joewing/q2/hardware/q2/pcb/q2/address.kicad_sch

## KiCad design hardware/q2/pcb/q2/address.kicad_sch (2024-12-15)

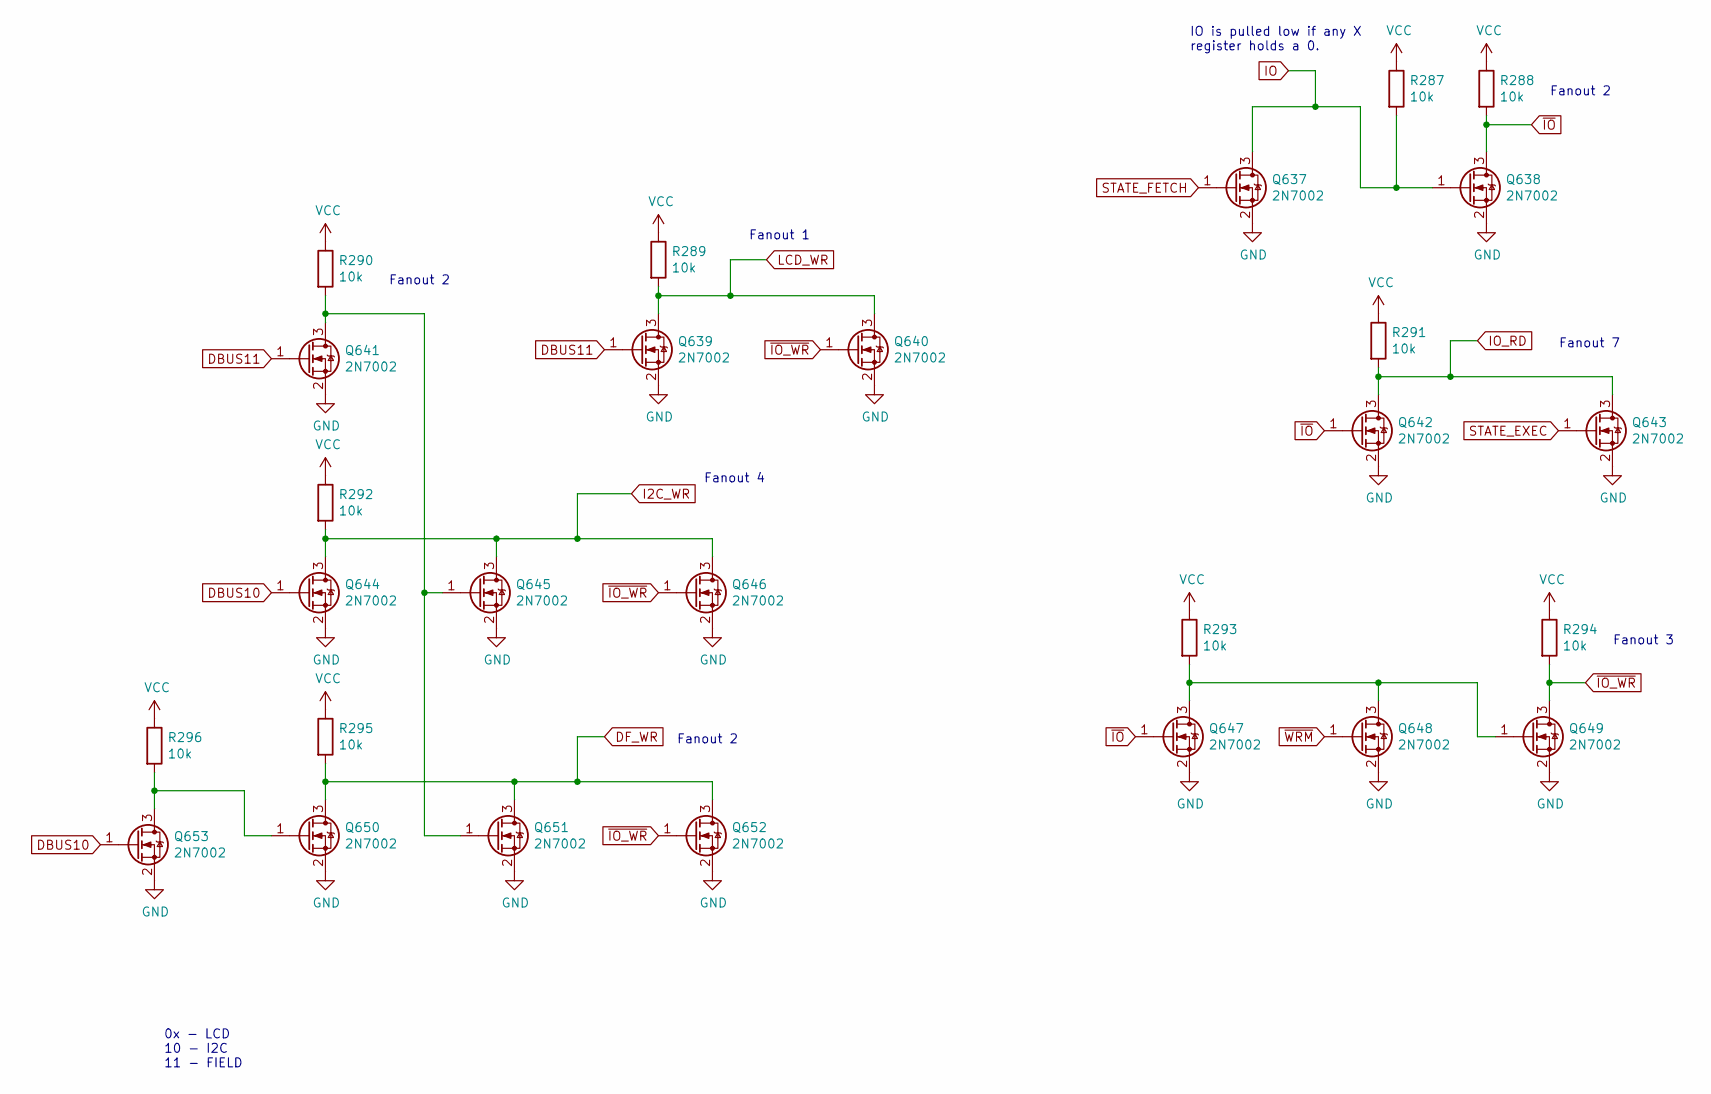
[picture p8: schematic address.kicad_sch]

Parts:
Q637, Q638, Q639, Q640, Q641, Q642, Q643, Q644, Q645, Q646, Q647, Q648, Q649, Q650, Q651, Q652, Q653: 2N7002; SOT-23; Part Number 2N7002; LCSC C181083
R287, R288, R289, R290, R291, R292, R293, R294, R295, R296: 10k; R_0603_1608Metric; Part Number 0603WAF1002T5E; LCSC C25804

Connections:
DBUS10: Q644.1 (G), Q653.1 (G)
DBUS11: Q639.1 (G), Q641.1 (G)
DF_WR: Q650.3 (D), Q651.3 (D), Q652.3 (D), R295.2
GND: Q637.2 (S), Q638.2 (S), Q639.2 (S), Q640.2 (S), Q641.2 (S), Q642.2 (S), Q643.2 (S), Q644.2 (S), Q645.2 (S), Q646.2 (S), Q647.2 (S), Q648.2 (S), Q649.2 (S), Q650.2 (S), Q651.2 (S), Q652.2 (S), Q653.2 (S)
I2C_WR: Q644.3 (D), Q645.3 (D), Q646.3 (D), R292.2
IO: Q637.3 (D), Q638.1 (G), R287.2
IO_RD: Q642.3 (D), Q643.3 (D), R291.2
LCD_WR: Q639.3 (D), Q640.3 (D), R289.2
unnamed: Q641.3 (D), Q645.1 (G), Q651.1 (G), R290.2
unnamed: Q647.3 (D), Q648.3 (D), Q649.1 (G), R293.2
unnamed: Q650.1 (G), Q653.3 (D), R296.2
STATE_EXEC: Q643.1 (G)
STATE_FETCH: Q637.1 (G)
VCC: R287.1, R288.1, R289.1, R290.1, R291.1, R292.1, R293.1, R294.1, R295.1, R296.1
~IO_WR: Q640.1 (G), Q646.1 (G), Q649.3 (D), Q652.1 (G), R294.2
~IO: Q638.3 (D), Q642.1 (G), Q647.1 (G), R288.2
~WRM: Q648.1 (G)

Notes on the sheet:
Fanout 2
Fanout 4
Fanout 3
0x - LCD 10 - I2C 11 - FIELD
IO is pulled low if any X register holds a 0.
Fanout 1
Fanout 7
