joewing/q2/hardware/q2/pcb/q2/alu.kicad_sch

## KiCad design hardware/q2/pcb/q2/alu.kicad_sch (2024-12-15)

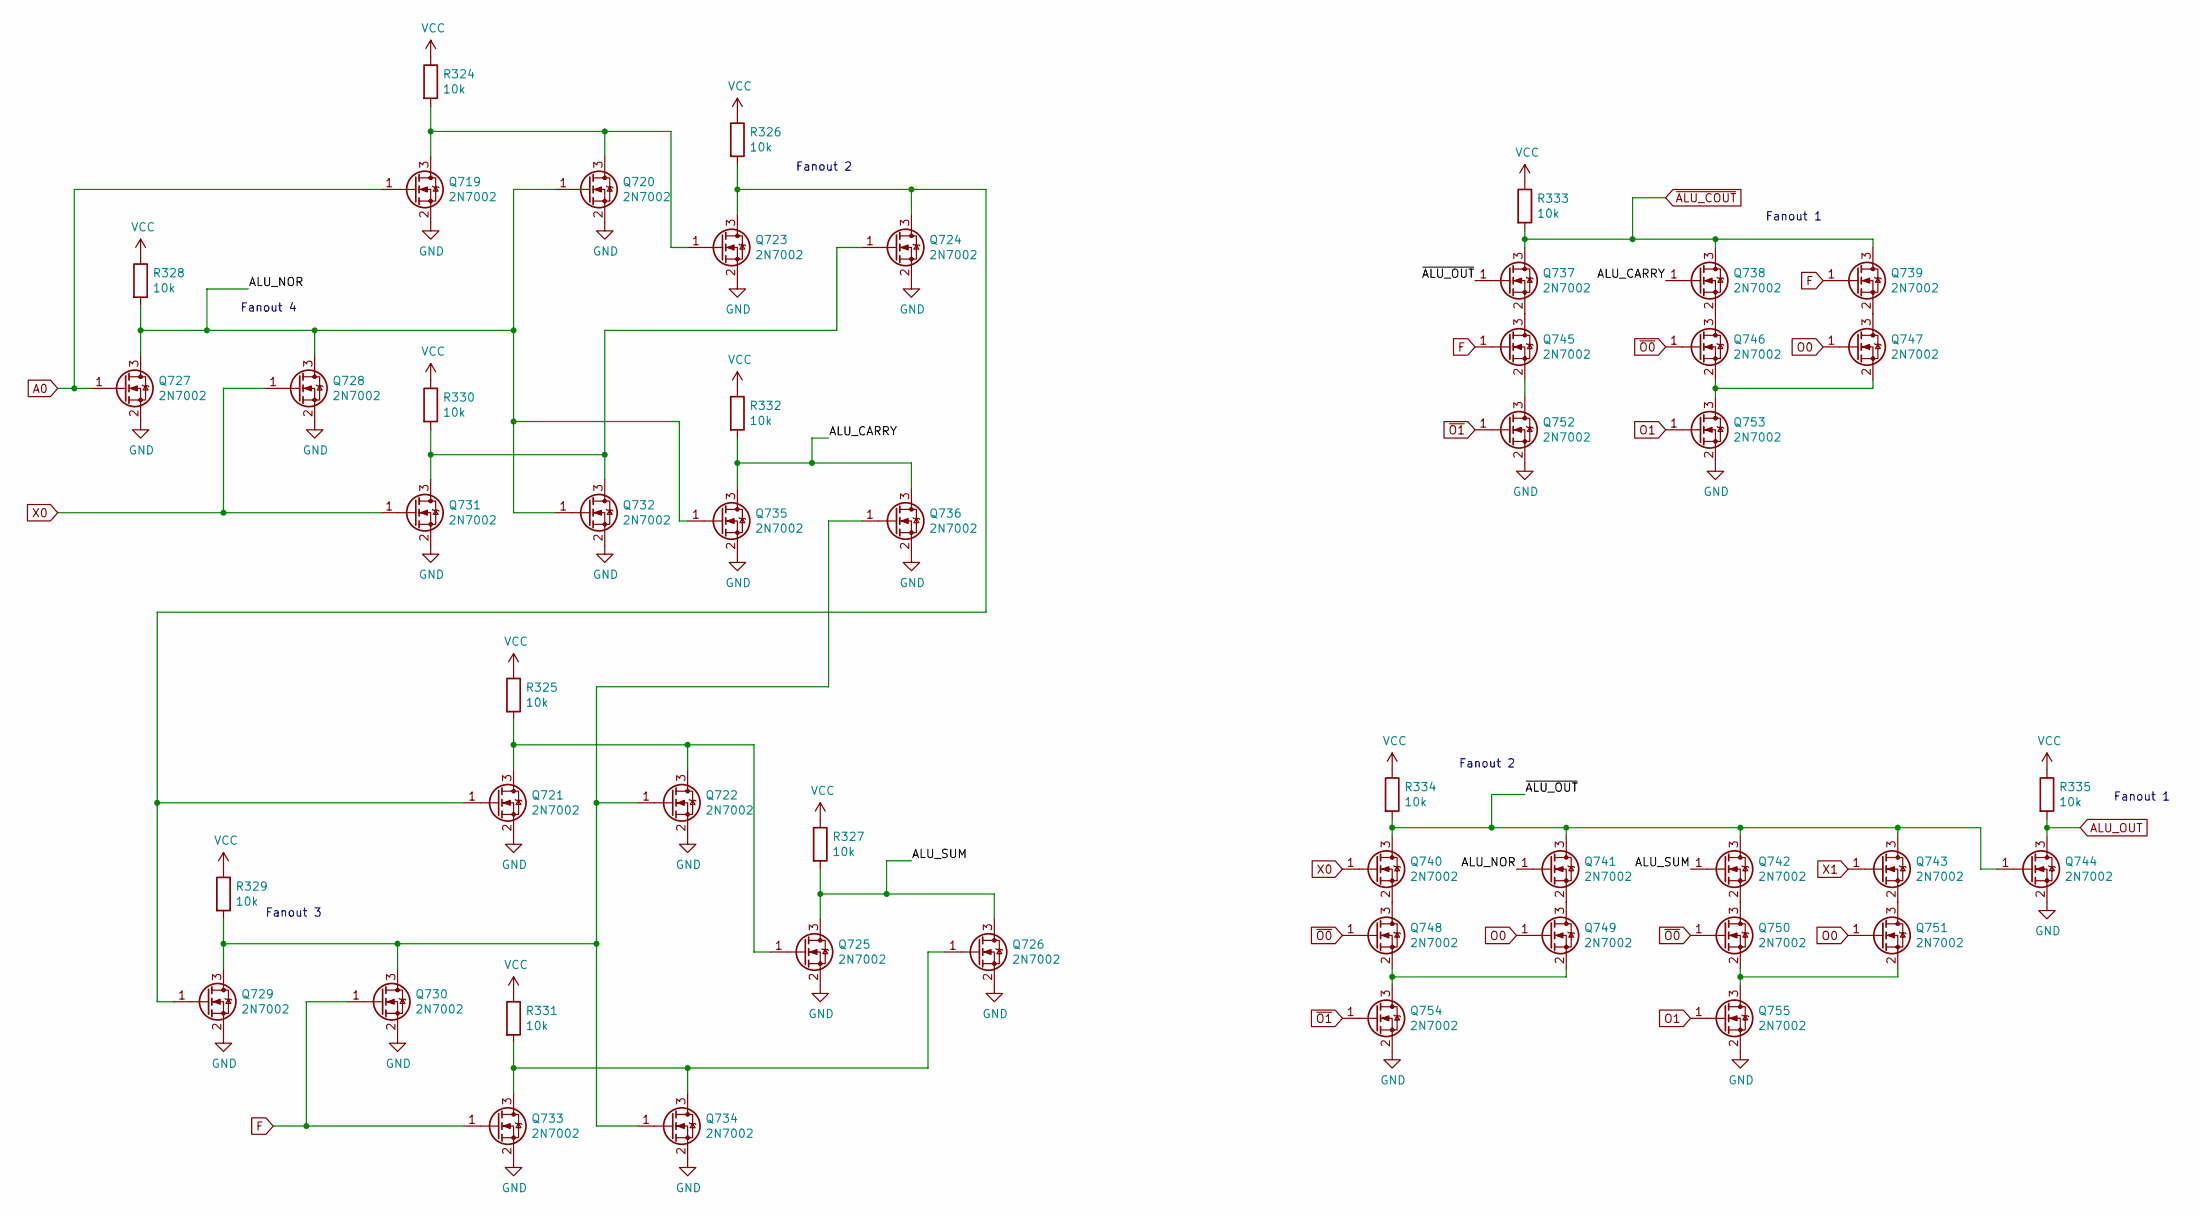
[picture p9: schematic alu.kicad_sch]

Parts:
Q719, Q720, Q721, Q722, Q723, Q724, Q725, Q726, Q727, Q728, Q729, Q730, Q731, Q732, Q733, Q734, Q735, Q736, Q737, Q738, Q739, Q740, Q741, Q742, Q743, Q744, Q745, Q746, Q747, Q748, Q749, Q750, Q751, Q752, Q753, Q754, Q755: 2N7002; SOT-23; Part Number 2N7002; LCSC C181083
R324, R325, R326, R327, R328, R329, R330, R331, R332, R333, R334, R335: 10k; R_0603_1608Metric; Part Number 0603WAF1002T5E; LCSC C25804

Connections:
A0: Q719.1 (G), Q727.1 (G)
ALU_CARRY: Q735.3 (D), Q736.3 (D), Q738.1 (G), R332.2
ALU_NOR: Q720.1 (G), Q727.3 (D), Q728.3 (D), Q732.1 (G), Q735.1 (G), Q741.1 (G), R328.2
ALU_OUT: Q744.3 (D), R335.2
ALU_SUM: Q725.3 (D), Q726.3 (D), Q742.1 (G), R327.2
F: Q730.1 (G), Q733.1 (G), Q739.1 (G), Q745.1 (G)
GND: Q719.2 (S), Q720.2 (S), Q721.2 (S), Q722.2 (S), Q723.2 (S), Q724.2 (S), Q725.2 (S), Q726.2 (S), Q727.2 (S), Q728.2 (S), Q729.2 (S), Q730.2 (S), Q731.2 (S), Q732.2 (S), Q733.2 (S), Q734.2 (S), Q735.2 (S), Q736.2 (S), Q744.2 (S), Q752.2 (S), Q753.2 (S), Q754.2 (S), Q755.2 (S)
unnamed: Q719.3 (D), Q720.3 (D), Q723.1 (G), R324.2
unnamed: Q721.1 (G), Q723.3 (D), Q724.3 (D), Q729.1 (G), R326.2
unnamed: Q721.3 (D), Q722.3 (D), Q725.1 (G), R325.2
unnamed: Q722.1 (G), Q729.3 (D), Q730.3 (D), Q734.1 (G), Q736.1 (G), R329.2
unnamed: Q724.1 (G), Q731.3 (D), Q732.3 (D), R330.2
unnamed: Q726.1 (G), Q733.3 (D), Q734.3 (D), R331.2
unnamed: Q737.2 (S), Q745.3 (D)
unnamed: Q738.2 (S), Q746.3 (D)
unnamed: Q739.2 (S), Q747.3 (D)
unnamed: Q740.2 (S), Q748.3 (D)
unnamed: Q741.2 (S), Q749.3 (D)
unnamed: Q742.2 (S), Q750.3 (D)
unnamed: Q743.2 (S), Q751.3 (D)
unnamed: Q745.2 (S), Q752.3 (D)
unnamed: Q746.2 (S), Q747.2 (S), Q753.3 (D)
unnamed: Q748.2 (S), Q749.2 (S), Q754.3 (D)
unnamed: Q750.2 (S), Q751.2 (S), Q755.3 (D)
O0: Q747.1 (G), Q749.1 (G), Q751.1 (G)
O1: Q753.1 (G), Q755.1 (G)
VCC: R324.1, R325.1, R326.1, R327.1, R328.1, R329.1, R330.1, R331.1, R332.1, R333.1, R334.1, R335.1
X0: Q728.1 (G), Q731.1 (G), Q740.1 (G)
X1: Q743.1 (G)
~ALU_COUT: Q737.3 (D), Q738.3 (D), Q739.3 (D), R333.2
~ALU_OUT: Q737.1 (G), Q740.3 (D), Q741.3 (D), Q742.3 (D), Q743.3 (D), Q744.1 (G), R334.2
~O0: Q746.1 (G), Q748.1 (G), Q750.1 (G)
~O1: Q752.1 (G), Q754.1 (G)

Notes on the sheet:
Fanout 2
Fanout 1
Fanout 3
Fanout 4
