joewing/q2/hardware/q2/pcb/q2/areg.kicad_sch

## KiCad design hardware/q2/pcb/q2/areg.kicad_sch (2024-12-15)

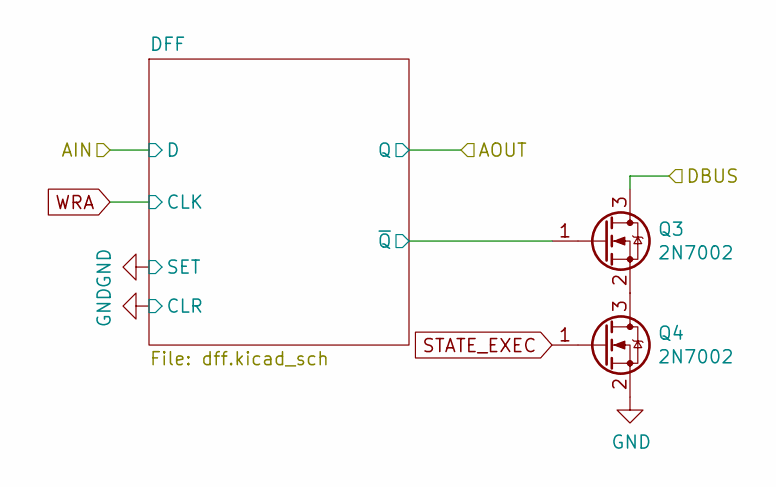
[picture p10: schematic areg.kicad_sch]

Parts:
Q3, Q4: 2N7002; SOT-23; Part Number 2N7002; LCSC C181083

Connections:
DBUS: Q3.3 (D)
GND: Q4.2 (S)
unnamed: Q3.2 (S), Q4.3 (D)
STATE_EXEC: Q4.1 (G)
~Q: Q3.1 (G)
