joewing/q2/hardware/q2/pcb/q2/clock.kicad_sch

## KiCad design hardware/q2/pcb/q2/clock.kicad_sch (2024-12-15)

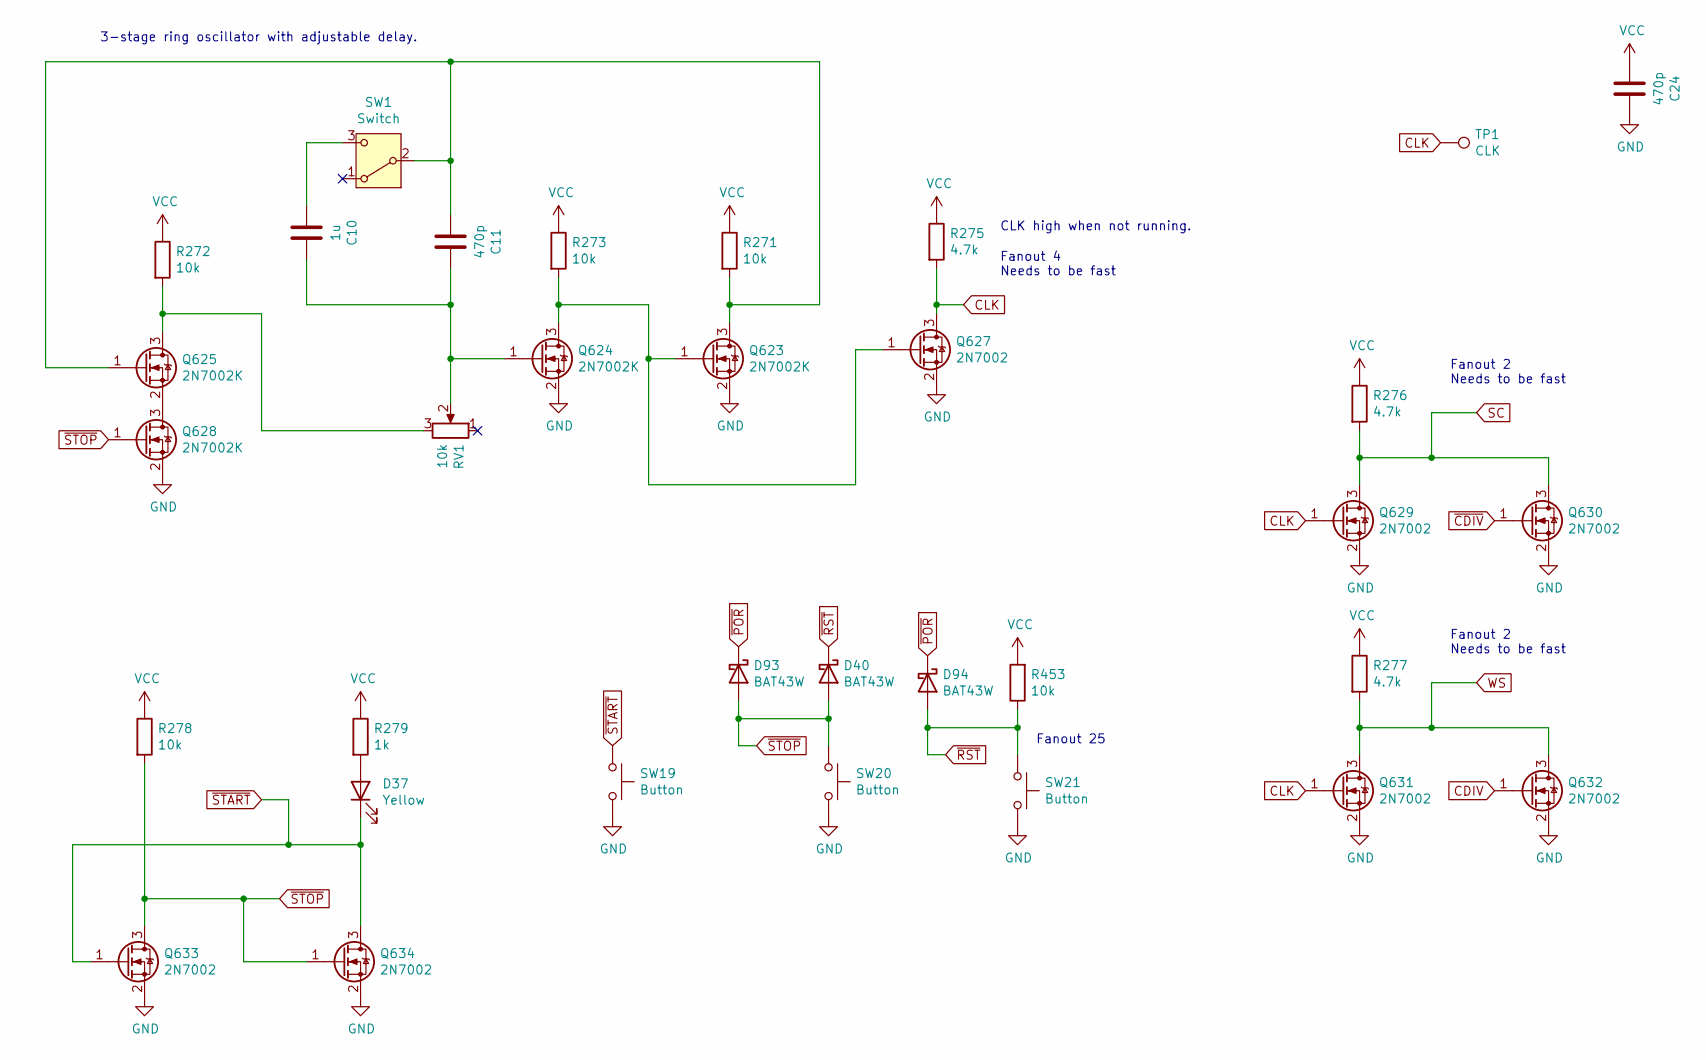
[picture p11: schematic clock.kicad_sch]

Parts:
C10: 1u; C_0805_2012Metric; Part Number CL21B105KBFNNNE; LCSC C28323
C11, C24: 470p; C_0805_2012Metric; Part Number 0805B471K500NT; LCSC C1743
D37: Yellow; LED_0805_2012Metric; Part Number 17-21SUYC/TR8; LCSC C2296
D40, D93, D94: BAT43W; D_SOD-123; Part Number BAT43W; LCSC C19167
Q623, Q624, Q625, Q628: 2N7002K; SOT-23; Part Number 2N7002K; LCSC C181083
Q627, Q629, Q630, Q631, Q632, Q633, Q634: 2N7002; SOT-23; Part Number 2N7002; LCSC C181083
R271, R272, R273, R278, R453: 10k; R_0603_1608Metric; Part Number 0603WAF1002T5E; LCSC C25804
R275, R276, R277: 4.7k; R_0603_1608Metric; Part Number 0603WAF4701T5E; LCSC C23162
R279: 1k; R_0603_1608Metric; Part Number 0603WAF1001T5E; LCSC C21190
RV1: 10k; Potentiometer_Bourns_3386P_Vertical; Part Number 3386P-1-103LF; LCSC C116281
SW1: Switch; TA-3524S-A2; Part Number TA-3524S-A2; LCSC C514017
SW19, SW20, SW21: Button; SW_SPST_PTS645; Part Number UK-B0228-G5-160-JZ; LCSC C620316
TP1: CLK; TestPoint_Loop_D2.50mm_Drill1.0mm

Connections:
CDIV: Q632.1 (G)
CLK: Q627.3 (D), Q629.1 (G), Q631.1 (G), R275.2, TP1.1
GND: C24.1, Q623.2 (S), Q624.2 (S), Q627.2 (S), Q628.2 (S), Q629.2 (S), Q630.2 (S), Q631.2 (S), Q632.2 (S), Q633.2 (S), Q634.2 (S), SW19.2, SW20.2, SW21.2
unnamed: C10.1, C11.1, Q624.1 (G), RV1.2
unnamed: C10.2, SW1.3 (C)
unnamed: C11.2, Q623.3 (D), Q625.1 (G), R271.2, SW1.2 (B)
unnamed: D37.2 (A), R279.2
unnamed: Q623.1 (G), Q624.3 (D), Q627.1 (G), R273.2
unnamed: Q625.2 (S), Q628.3 (D)
unnamed: Q625.3 (D), R272.2, RV1.3
SC: Q629.3 (D), Q630.3 (D), R276.2
VCC: C24.2, R271.1, R272.1, R273.1, R275.1, R276.1, R277.1, R278.1, R279.1, R453.2
WS: Q631.3 (D), Q632.3 (D), R277.2
~CDIV: Q630.1 (G)
~POR: D93.1 (K), D94.1 (K)
~RST: D40.1 (K), D94.2 (A), R453.1, SW21.1
~START: D37.1 (K), Q633.1 (G), Q634.3 (D), SW19.1
~STOP: D40.2 (A), D93.2 (A), Q628.1 (G), Q633.3 (D), Q634.1 (G), R278.2, SW20.1

Notes on the sheet:
Fanout 4 Needs to be fast
CLK high when not running.
Fanout 25
Fanout 2 Needs to be fast
3-stage ring oscillator with adjustable delay.
