joewing/q2/hardware/q2/pcb/q2/control.kicad_sch

## KiCad design hardware/q2/pcb/q2/control.kicad_sch (2024-12-15)

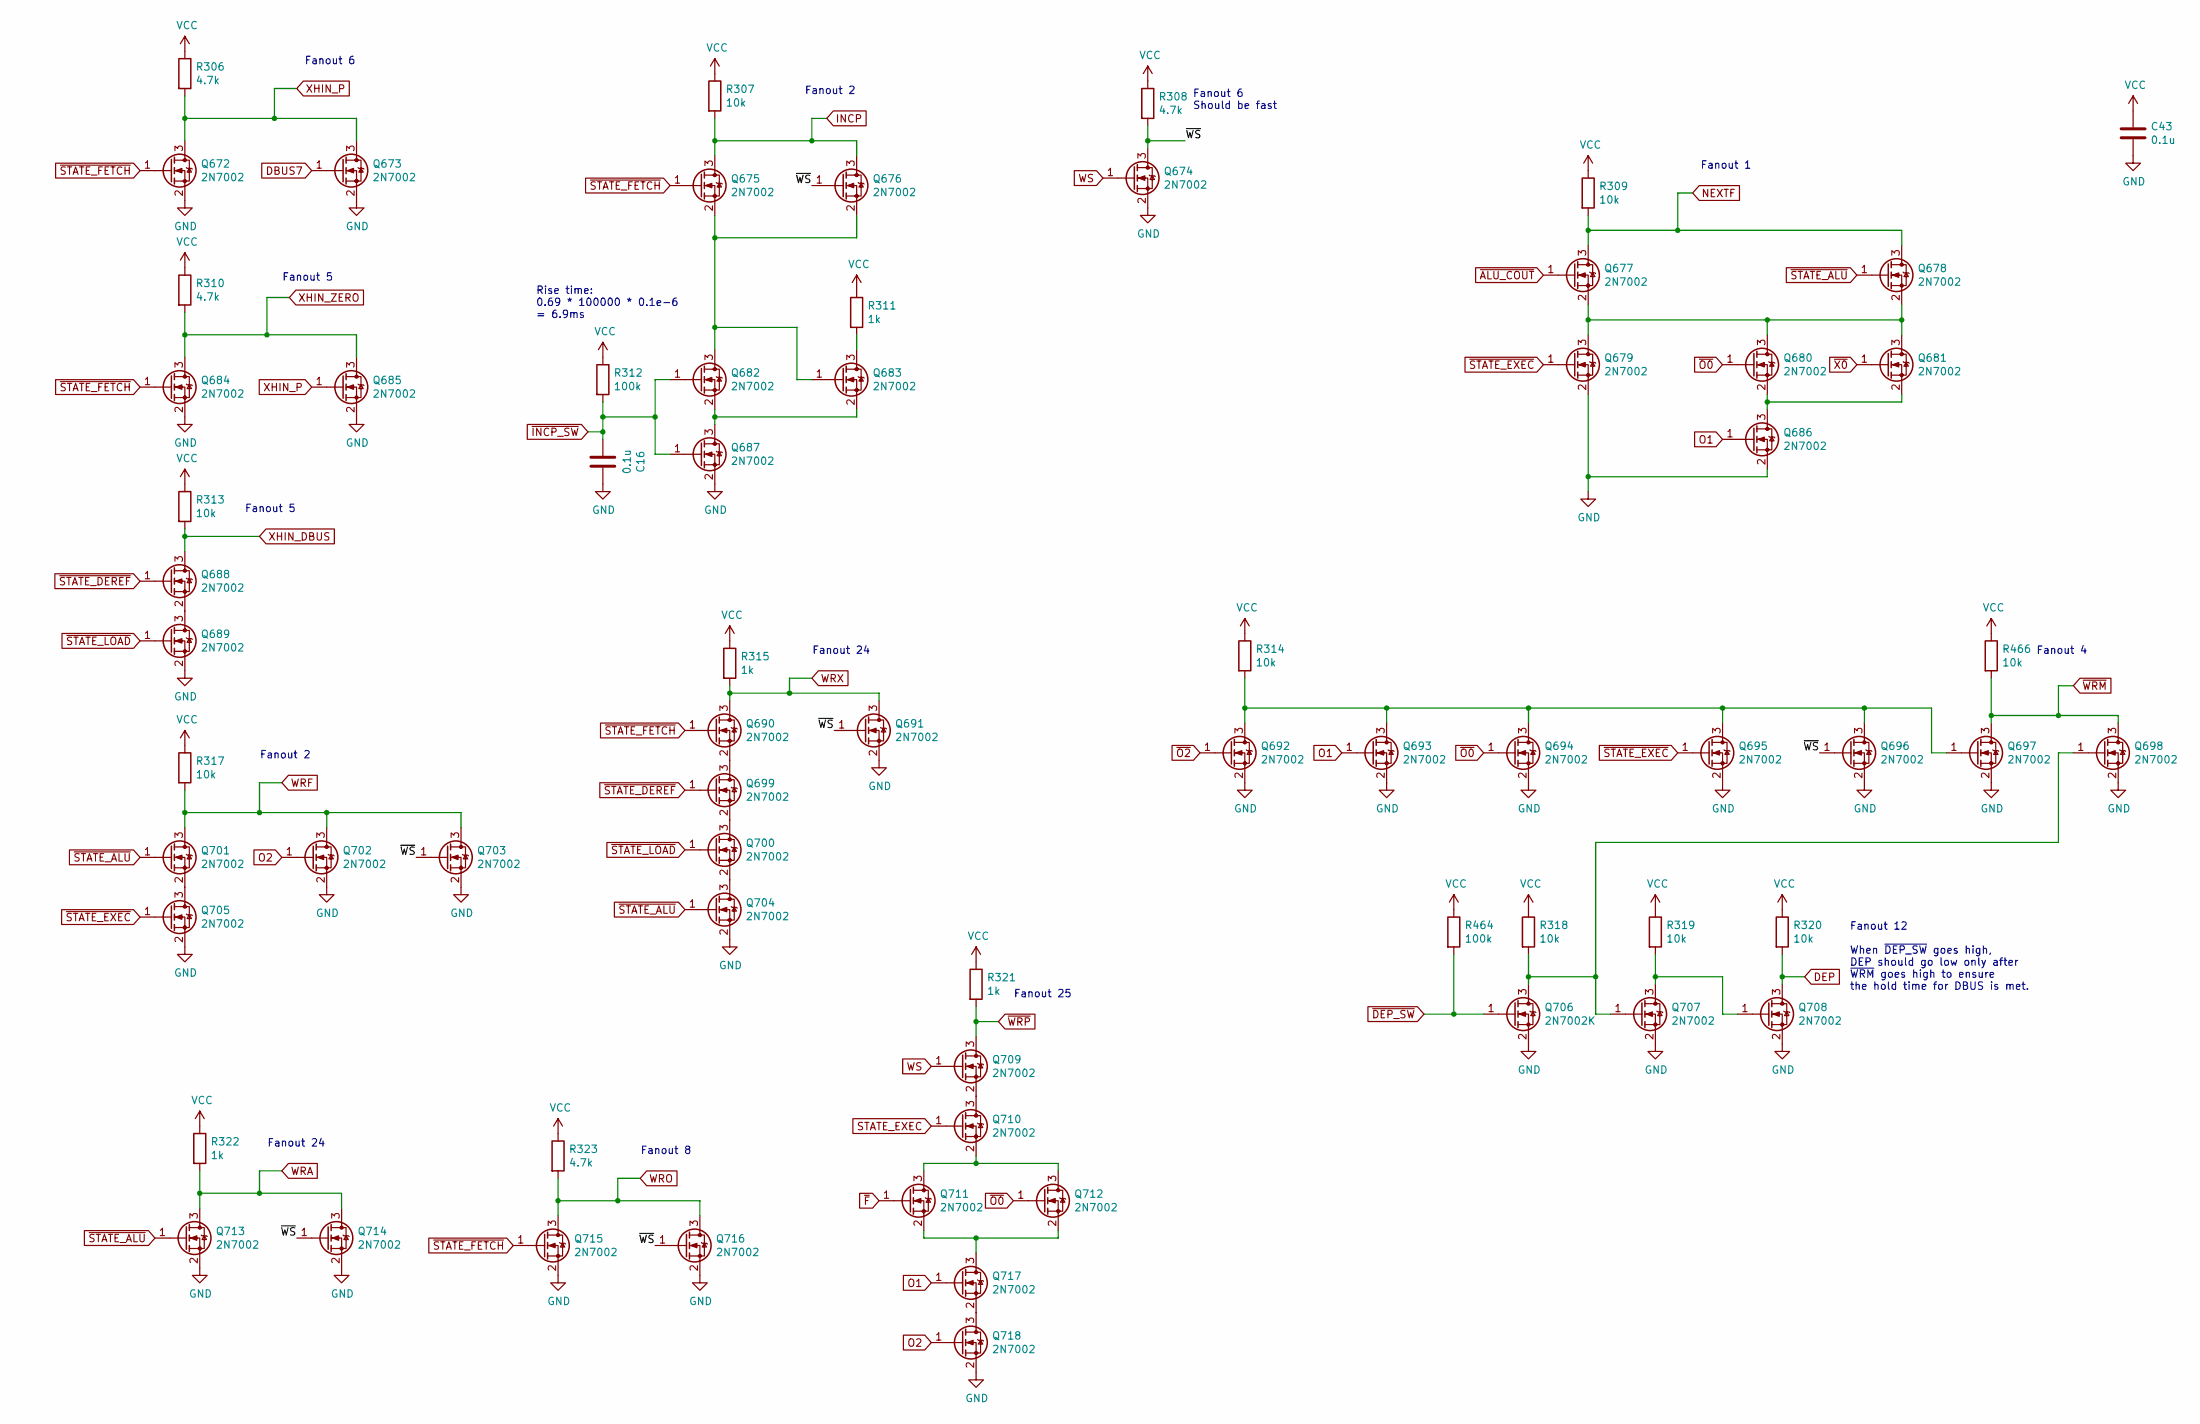
[picture p12: schematic control.kicad_sch]

Parts:
C16, C43: 0.1u; C_0805_2012Metric; Part Number CC0805KRX7R9BB104; LCSC C49678
Q672, Q673, Q674, Q675, Q676, Q677, Q678, Q679, Q680, Q681, Q682, Q683, Q684, Q685, Q686, Q687, Q688, Q689, Q690, Q691, Q692, Q693, Q694, Q695, Q696, Q697, Q698, Q699, Q700, Q701, Q702, Q703, Q704, Q705, Q707, Q708, Q709, Q710, Q711, Q712, Q713, Q714, Q715, Q716, Q717, Q718: 2N7002; SOT-23; Part Number 2N7002; LCSC C181083
Q706: 2N7002K; SOT-23; Part Number 2N7002K; LCSC C181083
R306, R308, R310, R323: 4.7k; R_0603_1608Metric; Part Number 0603WAF4701T5E; LCSC C23162
R307, R309, R313, R314, R317, R318, R319, R320, R466: 10k; R_0603_1608Metric; Part Number 0603WAF1002T5E; LCSC C25804
R311, R315, R321, R322: 1k; R_0603_1608Metric; Part Number 0603WAF1001T5E; LCSC C21190
R312, R464: 100k; R_0603_1608Metric; Part Number 0603WAF1003T5E; LCSC C25803

Connections:
DBUS7: Q673.1 (G)
DEP: Q708.3 (D), R320.2
GND: C16.1, C43.2, Q672.2 (S), Q673.2 (S), Q674.2 (S), Q679.2 (S), Q684.2 (S), Q685.2 (S), Q686.2 (S), Q687.2 (S), Q689.2 (S), Q691.2 (S), Q692.2 (S), Q693.2 (S), Q694.2 (S), Q695.2 (S), Q696.2 (S), Q697.2 (S), Q698.2 (S), Q702.2 (S), Q703.2 (S), Q704.2 (S), Q705.2 (S), Q706.2 (S), Q707.2 (S), Q708.2 (S), Q713.2 (S), Q714.2 (S), Q715.2 (S), Q716.2 (S), Q718.2 (S)
INCP: Q675.3 (D), Q676.3 (D), R307.2
NEXTF: Q677.3 (D), Q678.3 (D), R309.2
unnamed: Q675.2 (S), Q676.2 (S), Q682.3 (D), Q683.1 (G)
unnamed: Q677.2 (S), Q678.2 (S), Q679.3 (D), Q680.3 (D), Q681.3 (D)
unnamed: Q680.2 (S), Q681.2 (S), Q686.3 (D)
unnamed: Q682.2 (S), Q683.2 (S), Q687.3 (D)
unnamed: Q683.3 (D), R311.2
unnamed: Q688.2 (S), Q689.3 (D)
unnamed: Q690.2 (S), Q699.3 (D)
unnamed: Q692.3 (D), Q693.3 (D), Q694.3 (D), Q695.3 (D), Q696.3 (D), Q697.1 (G), R314.2
unnamed: Q698.1 (G), Q706.3 (D), Q707.1 (G), R318.2
unnamed: Q699.2 (S), Q700.3 (D)
unnamed: Q700.2 (S), Q704.3 (D)
unnamed: Q701.2 (S), Q705.3 (D)
unnamed: Q707.3 (D), Q708.1 (G), R319.2
unnamed: Q709.2 (S), Q710.3 (D)
unnamed: Q710.2 (S), Q711.3 (D), Q712.3 (D)
unnamed: Q711.2 (S), Q712.2 (S), Q717.3 (D)
unnamed: Q717.2 (S), Q718.3 (D)
O1: Q686.1 (G), Q693.1 (G), Q717.1 (G)
O2: Q702.1 (G), Q718.1 (G)
STATE_EXEC: Q710.1 (G)
VCC: C43.1, R306.1, R307.1, R308.1, R309.1, R310.1, R311.1, R312.1, R313.1, R314.1, R315.1, R317.1, R318.1, R319.1, R320.1, R321.1, R322.1, R323.1, R464.1, R466.1
WRA: Q713.3 (D), Q714.3 (D), R322.2
WRF: Q701.3 (D), Q702.3 (D), Q703.3 (D), R317.2
WRO: Q715.3 (D), Q716.3 (D), R323.2
WRX: Q690.3 (D), Q691.3 (D), R315.2
WS: Q674.1 (G), Q709.1 (G)
XHIN_DBUS: Q688.3 (D), R313.2
XHIN_P: Q672.3 (D), Q673.3 (D), Q685.1 (G), R306.2
XHIN_ZERO: Q684.3 (D), Q685.3 (D), R310.2
~ALU_COUT: Q677.1 (G)
~DEP_SW: Q706.1 (G), R464.2
~F: Q711.1 (G)
~INCP_SW: C16.2, Q682.1 (G), Q687.1 (G), R312.2
~O0: Q680.1 (G), Q694.1 (G), Q712.1 (G)
~O2: Q692.1 (G)
~STATE_ALU: Q678.1 (G), Q701.1 (G), Q704.1 (G), Q713.1 (G)
~STATE_DEREF: Q688.1 (G), Q699.1 (G)
~STATE_EXEC: Q679.1 (G), Q695.1 (G), Q705.1 (G)
~STATE_FETCH: Q672.1 (G), Q675.1 (G), Q684.1 (G), Q690.1 (G), Q715.1 (G)
~STATE_LOAD: Q689.1 (G), Q700.1 (G)
~WRM: Q697.3 (D), Q698.3 (D), R466.2
~WRP: Q709.3 (D), R321.2
~WS: Q674.3 (D), Q676.1 (G), Q691.1 (G), Q696.1 (G), Q703.1 (G), Q714.1 (G), Q716.1 (G), R308.2
~X0: Q681.1 (G)

Notes on the sheet:
Fanout 25
Fanout 4
Fanout 5
Fanout 24
Fanout 12 When ~{DEP_SW} goes high, DEP should go low only after ~{WRM} goes high to ensure the hold time for DBUS is met.
Fanout 2
Fanout 6 Should be fast
Fanout 6
Fanout 8
Rise time: 0.69 * 100000 * 0.1e-6 = 6.9ms
Fanout 1
