joewing/q2/hardware/q2/pcb/q2/decoder.kicad_sch

## KiCad design hardware/q2/pcb/q2/decoder.kicad_sch (2024-12-15)

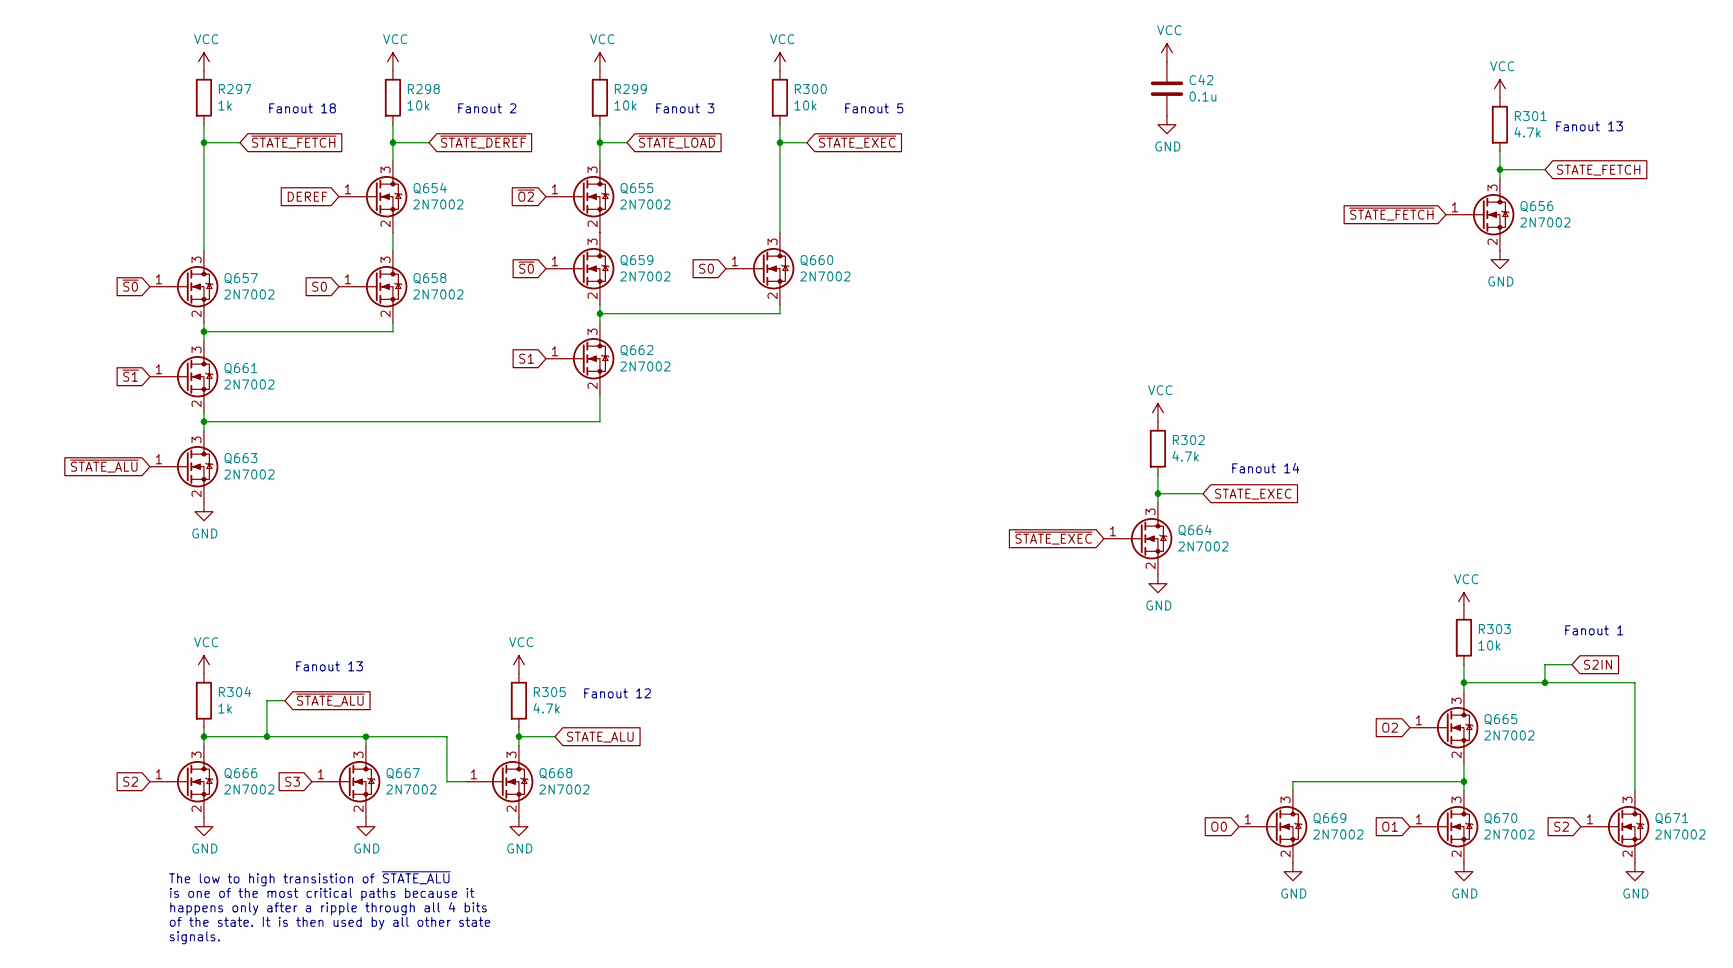
[picture p13: schematic decoder.kicad_sch]

Parts:
C42: 0.1u; C_0805_2012Metric; Part Number CC0805KRX7R9BB104; LCSC C49678
Q654, Q655, Q656, Q657, Q658, Q659, Q660, Q661, Q662, Q663, Q664, Q665, Q666, Q667, Q668, Q669, Q670, Q671: 2N7002; SOT-23; Part Number 2N7002; LCSC C181083
R297, R304: 1k; R_0603_1608Metric; Part Number 0603WAF1001T5E; LCSC C21190
R298, R299, R300, R303: 10k; R_0603_1608Metric; Part Number 0603WAF1002T5E; LCSC C25804
R301, R302, R305: 4.7k; R_0603_1608Metric; Part Number 0603WAF4701T5E; LCSC C23162

Connections:
DEREF: Q654.1 (G)
GND: C42.2, Q656.2 (S), Q663.2 (S), Q664.2 (S), Q666.2 (S), Q667.2 (S), Q668.2 (S), Q669.2 (S), Q670.2 (S), Q671.2 (S)
unnamed: Q654.2 (S), Q658.3 (D)
unnamed: Q655.2 (S), Q659.3 (D)
unnamed: Q657.2 (S), Q658.2 (S), Q661.3 (D)
unnamed: Q659.2 (S), Q660.2 (S), Q662.3 (D)
unnamed: Q661.2 (S), Q662.2 (S), Q663.3 (D)
unnamed: Q665.2 (S), Q669.3 (D), Q670.3 (D)
O0: Q669.1 (G)
O1: Q670.1 (G)
O2: Q665.1 (G)
S0: Q658.1 (G), Q660.1 (G)
S1: Q662.1 (G)
S2: Q666.1 (G), Q671.1 (G)
S2IN: Q665.3 (D), Q671.3 (D), R303.2
S3: Q667.1 (G)
STATE_ALU: Q668.3 (D), R305.2
STATE_EXEC: Q664.3 (D), R302.2
STATE_FETCH: Q656.3 (D), R301.2
VCC: C42.1, R297.1, R298.1, R299.1, R300.1, R301.1, R302.1, R303.1, R304.1, R305.1
~O2: Q655.1 (G)
~S0: Q657.1 (G), Q659.1 (G)
~S1: Q661.1 (G)
~STATE_ALU: Q663.1 (G), Q666.3 (D), Q667.3 (D), Q668.1 (G), R304.2
~STATE_DEREF: Q654.3 (D), R298.2
~STATE_EXEC: Q660.3 (D), Q664.1 (G), R300.2
~STATE_FETCH: Q656.1 (G), Q657.3 (D), R297.2
~STATE_LOAD: Q655.3 (D), R299.2

Notes on the sheet:
Fanout 13
Fanout 14
Fanout 12
Fanout 2
Fanout 1
The low to high transistion of ~{STATE_ALU} is one of the most critical paths because it happens only after a ripple through all 4 bits of the state. It is then used by all other state signals.
Fanout 5
Fanout 3
Fanout 18
