joewing/q2/hardware/q2/pcb/q2/dff.kicad_sch

## KiCad design hardware/q2/pcb/q2/dff.kicad_sch (2024-12-15)

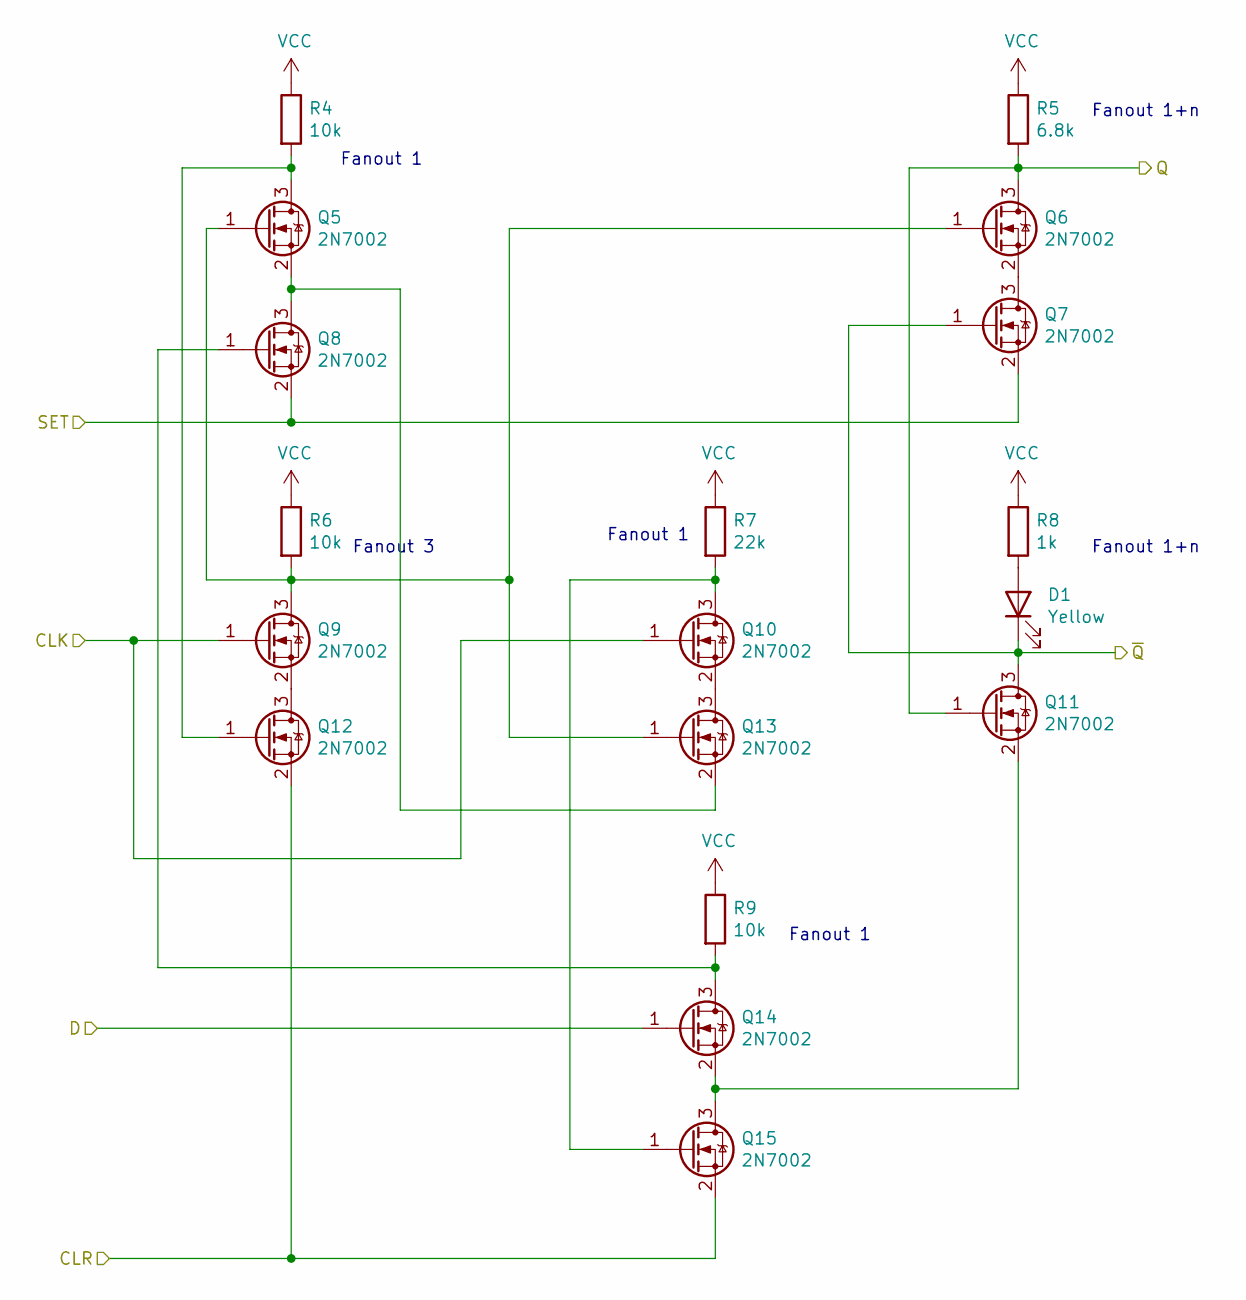
[picture p14: schematic dff.kicad_sch]

Parts:
D1: Yellow; LED_0805_2012Metric; Part Number 17-21SUYC/TR8; LCSC C2296
Q5, Q6, Q7, Q8, Q9, Q10, Q11, Q12, Q13, Q14, Q15: 2N7002; SOT-23; Part Number 2N7002; LCSC C181083
R4, R6, R9: 10k; R_0603_1608Metric; Part Number 0603WAF1002T5E; LCSC C25804
R5: 6.8k; R_0603_1608Metric; Part Number 0603WAF6801T5E; LCSC C23212
R7: 22k; R_0603_1608Metric; Part Number 0603WAF2202T5E; LCSC C31850
R8: 1k; R_0603_1608Metric; Part Number 0603WAF1001T5E; LCSC C21190

Connections:
CLK: Q9.1 (G), Q10.1 (G)
CLR: Q12.2 (S), Q15.2 (S)
D: Q14.1 (G)
unnamed: D1.2 (A), R8.2
unnamed: Q6.2 (S), Q7.3 (D)
unnamed: Q10.2 (S), Q13.3 (D)
unnamed: Q10.3 (D), Q15.1 (G), R7.2
unnamed: Q11.2 (S), Q14.2 (S), Q15.3 (D)
unnamed: Q5.3 (D), Q12.1 (G), R4.2
unnamed: Q9.2 (S), Q12.3 (D)
unnamed: Q5.1 (G), Q6.1 (G), Q9.3 (D), Q13.1 (G), R6.2
unnamed: Q5.2 (S), Q8.3 (D), Q13.2 (S)
unnamed: Q8.1 (G), Q14.3 (D), R9.2
Q: Q6.3 (D), Q11.1 (G), R5.2
SET: Q7.2 (S), Q8.2 (S)
VCC: R4.1, R5.1, R6.1, R7.1, R8.1, R9.1
~Q: D1.1 (K), Q7.1 (G), Q11.3 (D)

Notes on the sheet:
Fanout 1+n
Fanout 1
Fanout 3
