joewing/q2/hardware/q2/pcb/q2/field.kicad_sch

## KiCad design hardware/q2/pcb/q2/field.kicad_sch (2024-12-15)

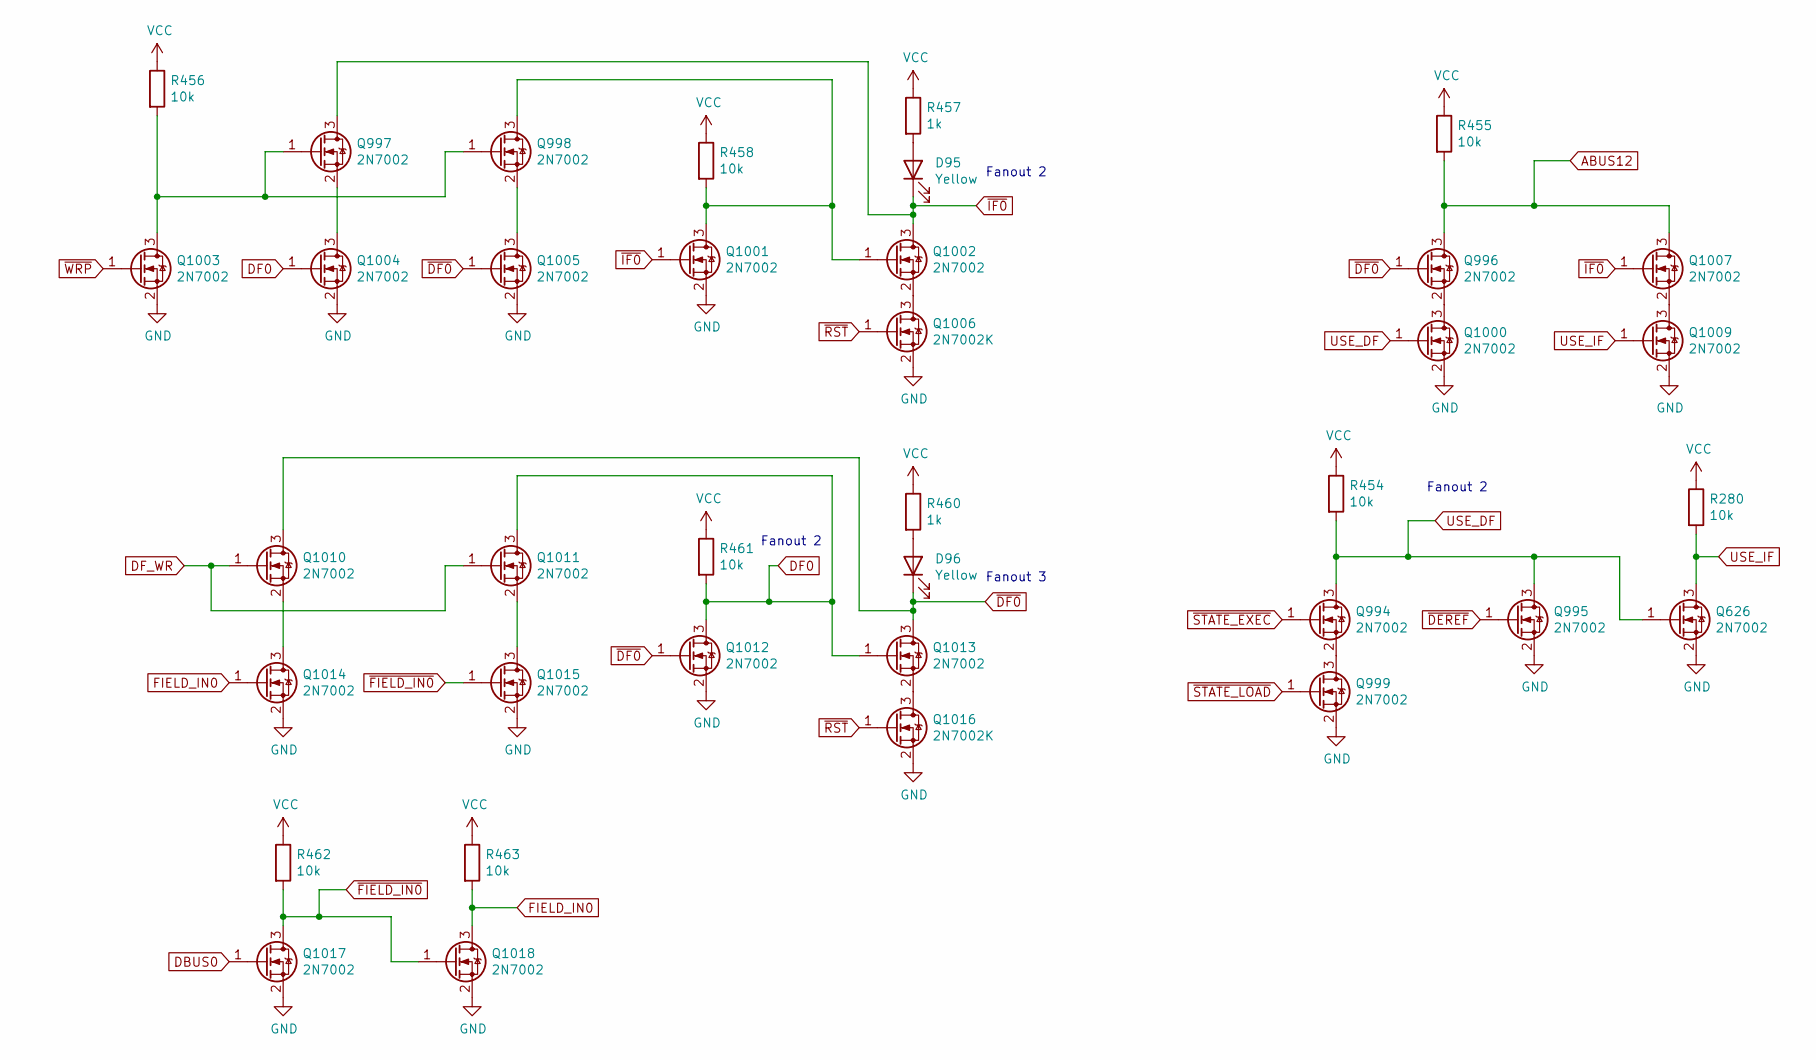
[picture p15: schematic field.kicad_sch]

Parts:
D95, D96: Yellow; LED_0805_2012Metric; Part Number 17-21SUYC/TR8; LCSC C2296
Q626, Q994, Q995, Q996, Q997, Q998, Q999, Q1000, Q1001, Q1002, Q1003, Q1004, Q1005, Q1007, Q1009, Q1010, Q1011, Q1012, Q1013, Q1014, Q1015, Q1017, Q1018: 2N7002; SOT-23; Part Number 2N7002; LCSC C181083
Q1006, Q1016: 2N7002K; SOT-23; Part Number 2N7002K; LCSC C181083
R280, R454, R455, R456, R458, R461, R462, R463: 10k; R_0603_1608Metric; Part Number 0603WAF1002T5E; LCSC C25804
R457, R460: 1k; R_0603_1608Metric; Part Number 0603WAF1001T5E; LCSC C21190

Connections:
ABUS12: Q996.3 (D), Q1007.3 (D), R455.2
DBUS0: Q1017.1 (G)
DF0: Q1004.1 (G), Q1011.3 (D), Q1012.3 (D), Q1013.1 (G), R461.2
DF_WR: Q1010.1 (G), Q1011.1 (G)
FIELD_IN0: Q1014.1 (G), Q1018.3 (D), R463.2
GND: Q626.2 (S), Q995.2 (S), Q999.2 (S), Q1000.2 (S), Q1001.2 (S), Q1003.2 (S), Q1004.2 (S), Q1005.2 (S), Q1006.2 (S), Q1009.2 (S), Q1012.2 (S), Q1014.2 (S), Q1015.2 (S), Q1016.2 (S), Q1017.2 (S), Q1018.2 (S)
unnamed: D95.2 (A), R457.2
unnamed: D96.2 (A), R460.2
unnamed: Q994.2 (S), Q999.3 (D)
unnamed: Q996.2 (S), Q1000.3 (D)
unnamed: Q998.3 (D), Q1001.3 (D), Q1002.1 (G), R458.2
unnamed: Q1002.2 (S), Q1006.3 (D)
unnamed: Q997.1 (G), Q998.1 (G), Q1003.3 (D), R456.2
unnamed: Q997.2 (S), Q1004.3 (D)
unnamed: Q998.2 (S), Q1005.3 (D)
unnamed: Q1007.2 (S), Q1009.3 (D)
unnamed: Q1010.2 (S), Q1014.3 (D)
unnamed: Q1011.2 (S), Q1015.3 (D)
unnamed: Q1013.2 (S), Q1016.3 (D)
USE_DF: Q626.1 (G), Q994.3 (D), Q995.3 (D), Q1000.1 (G), R454.2
USE_IF: Q626.3 (D), Q1009.1 (G), R280.2
VCC: R280.1, R454.1, R455.1, R456.1, R457.1, R458.1, R460.1, R461.1, R462.1, R463.1
~DEREF: Q995.1 (G)
~DF0: D96.1 (K), Q996.1 (G), Q1005.1 (G), Q1010.3 (D), Q1012.1 (G), Q1013.3 (D)
~FIELD_IN0: Q1015.1 (G), Q1017.3 (D), Q1018.1 (G), R462.2
~IF0: D95.1 (K), Q997.3 (D), Q1001.1 (G), Q1002.3 (D), Q1007.1 (G)
~RST: Q1006.1 (G), Q1016.1 (G)
~STATE_EXEC: Q994.1 (G)
~STATE_LOAD: Q999.1 (G)
~WRP: Q1003.1 (G)

Notes on the sheet:
Fanout 2
Fanout 3
