joewing/q2/hardware/q2/pcb/q2/frontpanel.kicad_sch

## KiCad design hardware/q2/pcb/q2/frontpanel.kicad_sch (2024-12-15)

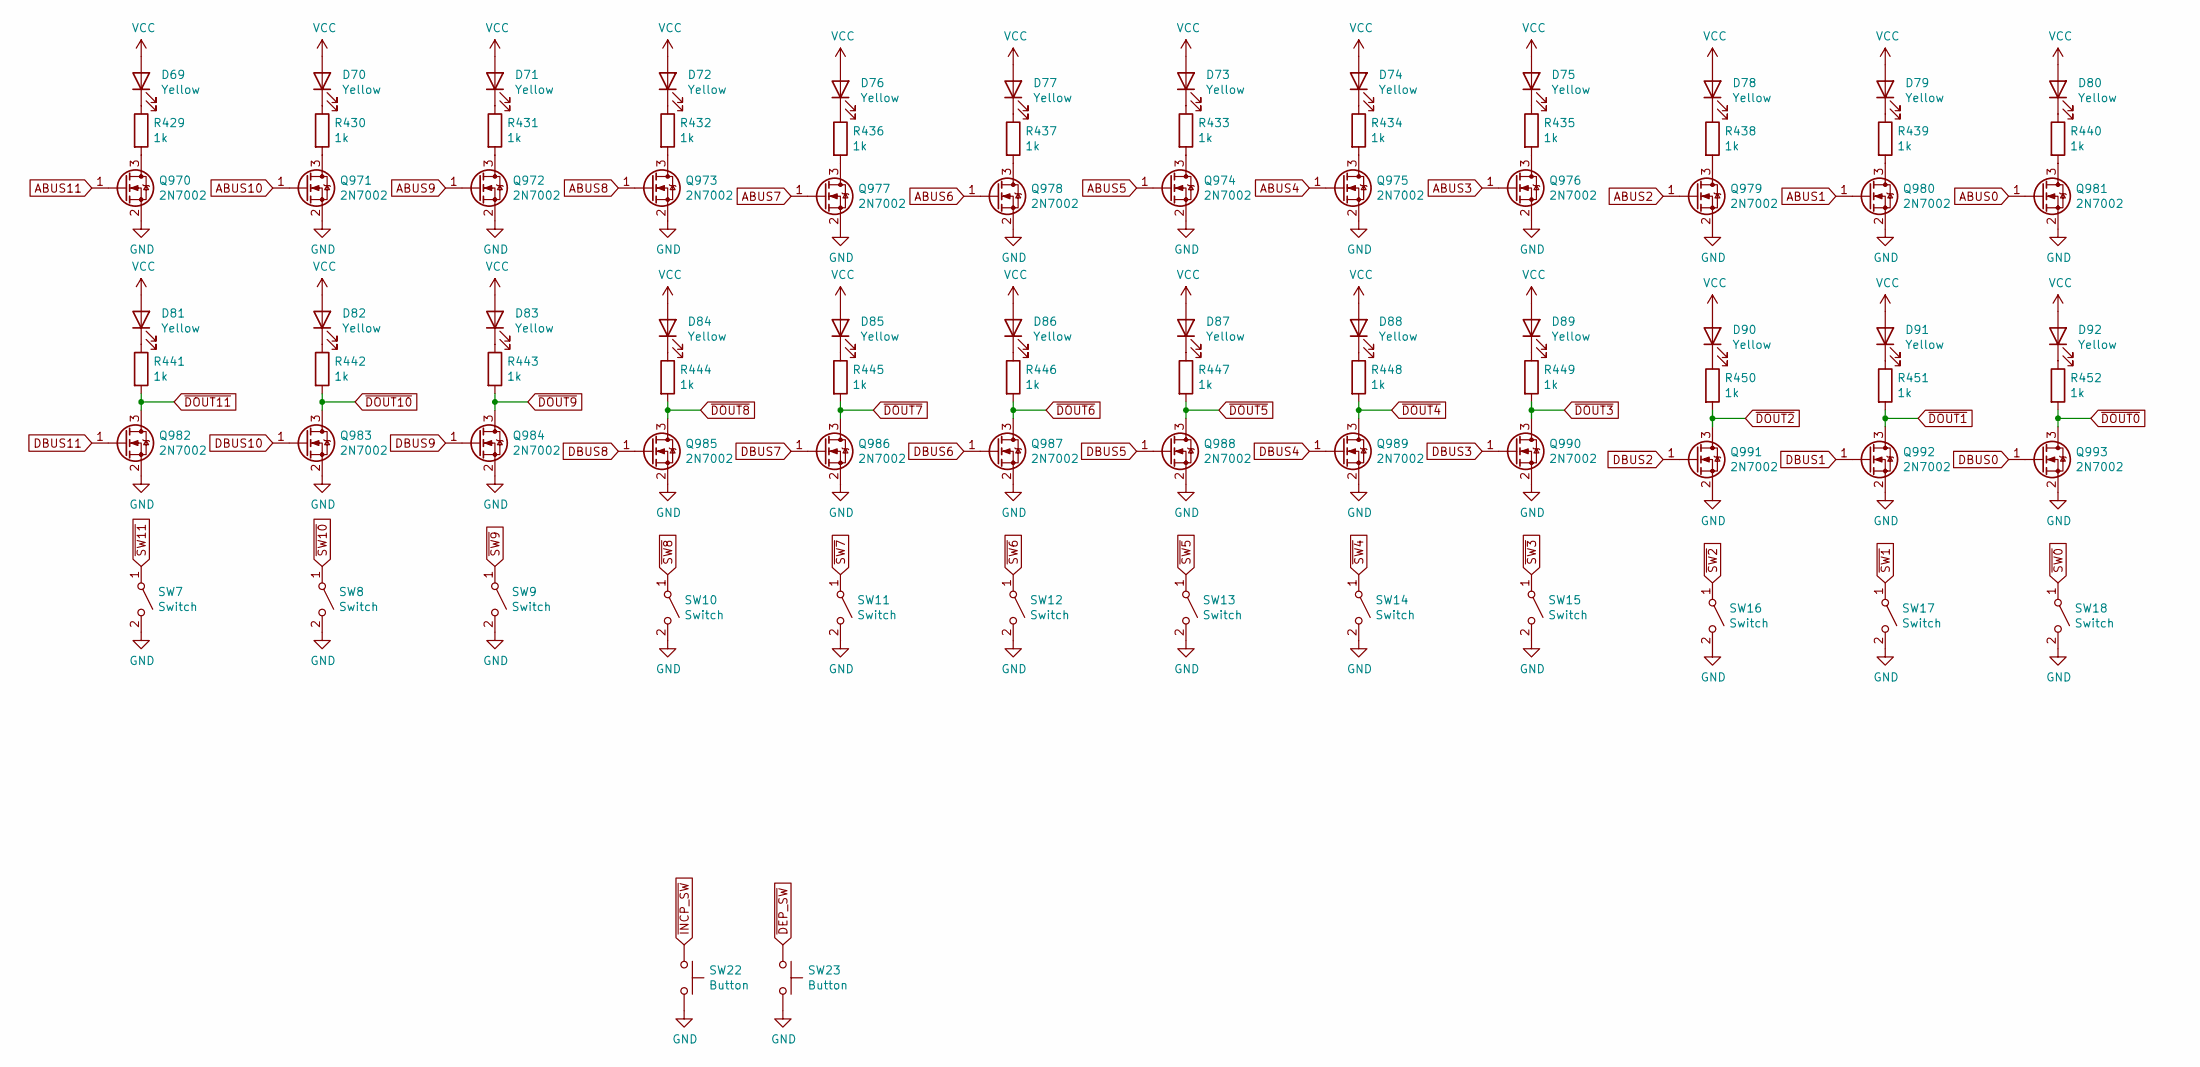
[picture p16: schematic frontpanel.kicad_sch]

Parts:
D69, D70, D71, D72, D73, D74, D75, D76, D77, D78, D79, D80, D81, D82, D83, D84, D85, D86, D87, D88, D89, D90, D91, D92: Yellow; LED_0805_2012Metric; Part Number 17-21SUYC/TR8; LCSC C2296
Q970, Q971, Q972, Q973, Q974, Q975, Q976, Q977, Q978, Q979, Q980, Q981, Q982, Q983, Q984, Q985, Q986, Q987, Q988, Q989, Q990, Q991, Q992, Q993: 2N7002; SOT-23; Part Number 2N7002; LCSC C181083
R429, R430, R431, R432, R433, R434, R435, R436, R437, R438, R439, R440, R441, R442, R443, R444, R445, R446, R447, R448, R449, R450, R451, R452: 1k; R_0603_1608Metric; Part Number 0603WAF1001T5E; LCSC C21190
SW7, SW8, SW9, SW10, SW11, SW12, SW13, SW14, SW15, SW16, SW17, SW18: Switch; TA-3524S-A2; Part Number TA-3524S-A2; LCSC C514017
SW22, SW23: Button; SW_SPST_PTS645; Part Number UK-B0228-G5-160-JZ; LCSC C620316

Connections:
ABUS0: Q981.1 (G)
ABUS1: Q980.1 (G)
ABUS2: Q979.1 (G)
ABUS3: Q976.1 (G)
ABUS4: Q975.1 (G)
ABUS5: Q974.1 (G)
ABUS6: Q978.1 (G)
ABUS7: Q977.1 (G)
ABUS8: Q973.1 (G)
ABUS9: Q972.1 (G)
ABUS10: Q971.1 (G)
ABUS11: Q970.1 (G)
DBUS0: Q993.1 (G)
DBUS1: Q992.1 (G)
DBUS2: Q991.1 (G)
DBUS3: Q990.1 (G)
DBUS4: Q989.1 (G)
DBUS5: Q988.1 (G)
DBUS6: Q987.1 (G)
DBUS7: Q986.1 (G)
DBUS8: Q985.1 (G)
DBUS9: Q984.1 (G)
DBUS10: Q983.1 (G)
DBUS11: Q982.1 (G)
GND: Q970.2 (S), Q971.2 (S), Q972.2 (S), Q973.2 (S), Q974.2 (S), Q975.2 (S), Q976.2 (S), Q977.2 (S), Q978.2 (S), Q979.2 (S), Q980.2 (S), Q981.2 (S), Q982.2 (S), Q983.2 (S), Q984.2 (S), Q985.2 (S), Q986.2 (S), Q987.2 (S), Q988.2 (S), Q989.2 (S), Q990.2 (S), Q991.2 (S), Q992.2 (S), Q993.2 (S), SW7.2 (B), SW8.2 (B), SW9.2 (B), SW10.2 (B), SW11.2 (B), SW12.2 (B), SW13.2 (B), SW14.2 (B), SW15.2 (B), SW16.2 (B), SW17.2 (B), SW18.2 (B), SW22.2, SW23.2
unnamed: D69.1 (K), R429.1
unnamed: D70.1 (K), R430.1
unnamed: D71.1 (K), R431.1
unnamed: D72.1 (K), R432.1
unnamed: D73.1 (K), R433.1
unnamed: D74.1 (K), R434.1
unnamed: D75.1 (K), R435.1
unnamed: D76.1 (K), R436.1
unnamed: D77.1 (K), R437.1
unnamed: D78.1 (K), R438.1
unnamed: D79.1 (K), R439.1
unnamed: D80.1 (K), R440.1
unnamed: D81.1 (K), R441.1
unnamed: D82.1 (K), R442.1
unnamed: D83.1 (K), R443.1
unnamed: D84.1 (K), R444.1
unnamed: D85.1 (K), R445.1
unnamed: D86.1 (K), R446.1
unnamed: D87.1 (K), R447.1
unnamed: D88.1 (K), R448.1
unnamed: D89.1 (K), R449.1
unnamed: D90.1 (K), R450.1
unnamed: D91.1 (K), R451.1
unnamed: D92.1 (K), R452.1
unnamed: Q970.3 (D), R429.2
unnamed: Q971.3 (D), R430.2
unnamed: Q972.3 (D), R431.2
unnamed: Q973.3 (D), R432.2
unnamed: Q974.3 (D), R433.2
unnamed: Q975.3 (D), R434.2
unnamed: Q976.3 (D), R435.2
unnamed: Q977.3 (D), R436.2
unnamed: Q978.3 (D), R437.2
unnamed: Q979.3 (D), R438.2
unnamed: Q980.3 (D), R439.2
unnamed: Q981.3 (D), R440.2
VCC: D69.2 (A), D70.2 (A), D71.2 (A), D72.2 (A), D73.2 (A), D74.2 (A), D75.2 (A), D76.2 (A), D77.2 (A), D78.2 (A), D79.2 (A), D80.2 (A), D81.2 (A), D82.2 (A), D83.2 (A), D84.2 (A), D85.2 (A), D86.2 (A), D87.2 (A), D88.2 (A), D89.2 (A), D90.2 (A), D91.2 (A), D92.2 (A)
~DEP_SW: SW23.1
~DOUT0: Q993.3 (D), R452.2
~DOUT1: Q992.3 (D), R451.2
~DOUT2: Q991.3 (D), R450.2
~DOUT3: Q990.3 (D), R449.2
~DOUT4: Q989.3 (D), R448.2
~DOUT5: Q988.3 (D), R447.2
~DOUT6: Q987.3 (D), R446.2
~DOUT7: Q986.3 (D), R445.2
~DOUT8: Q985.3 (D), R444.2
~DOUT9: Q984.3 (D), R443.2
~DOUT10: Q983.3 (D), R442.2
~DOUT11: Q982.3 (D), R441.2
~INCP_SW: SW22.1
~SW0: SW18.1 (A)
~SW1: SW17.1 (A)
~SW2: SW16.1 (A)
~SW3: SW15.1 (A)
~SW4: SW14.1 (A)
~SW5: SW13.1 (A)
~SW6: SW12.1 (A)
~SW7: SW11.1 (A)
~SW8: SW10.1 (A)
~SW9: SW9.1 (A)
~SW10: SW8.1 (A)
~SW11: SW7.1 (A)
