joewing/q2/hardware/q2/pcb/q2/i2c.kicad_sch

## KiCad design hardware/q2/pcb/q2/i2c.kicad_sch (2024-12-15)

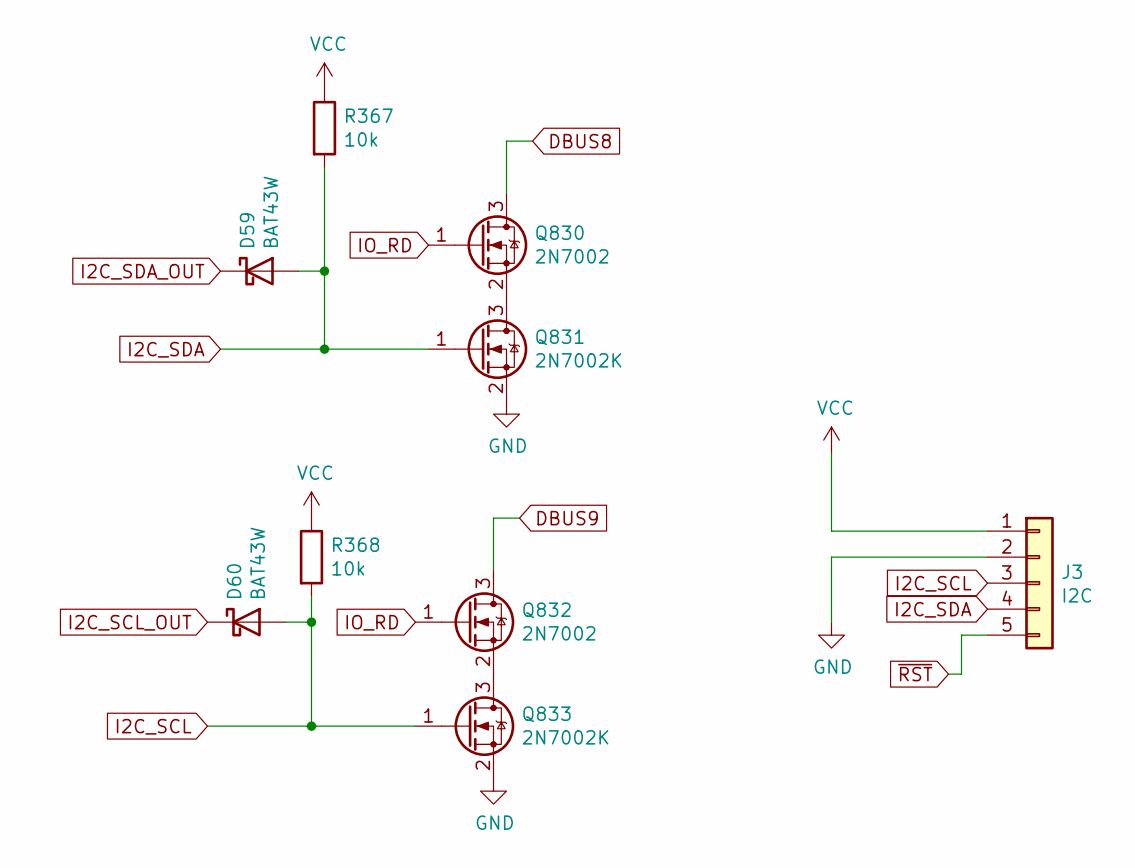
[picture p17: schematic i2c.kicad_sch]

Parts:
D59, D60: BAT43W; D_SOD-123; Part Number BAT43W; LCSC C19167
J3: I2C; PinHeader_1x05_P2.54mm_Horizontal
Q830, Q832: 2N7002; SOT-23; Part Number 2N7002; LCSC C181083
Q831, Q833: 2N7002K; SOT-23; Part Number 2N7002K; LCSC C181083
R367, R368: 10k; R_0603_1608Metric; Part Number 0603WAF1002T5E; LCSC C25804

Connections:
DBUS8: Q830.3 (D)
DBUS9: Q832.3 (D)
GND: J3.2, Q831.2 (S), Q833.2 (S)
I2C_SCL: D60.2 (A), J3.3, Q833.1 (G), R368.2
I2C_SCL_OUT: D60.1 (K)
I2C_SDA: D59.2 (A), J3.4, Q831.1 (G), R367.2
I2C_SDA_OUT: D59.1 (K)
IO_RD: Q830.1 (G), Q832.1 (G)
unnamed: Q830.2 (S), Q831.3 (D)
unnamed: Q832.2 (S), Q833.3 (D)
VCC: J3.1, R367.1, R368.1
~RST: J3.5
