joewing/q2/hardware/q2/pcb/q2/memory.kicad_sch

## KiCad design hardware/q2/pcb/q2/memory.kicad_sch (2024-12-15)

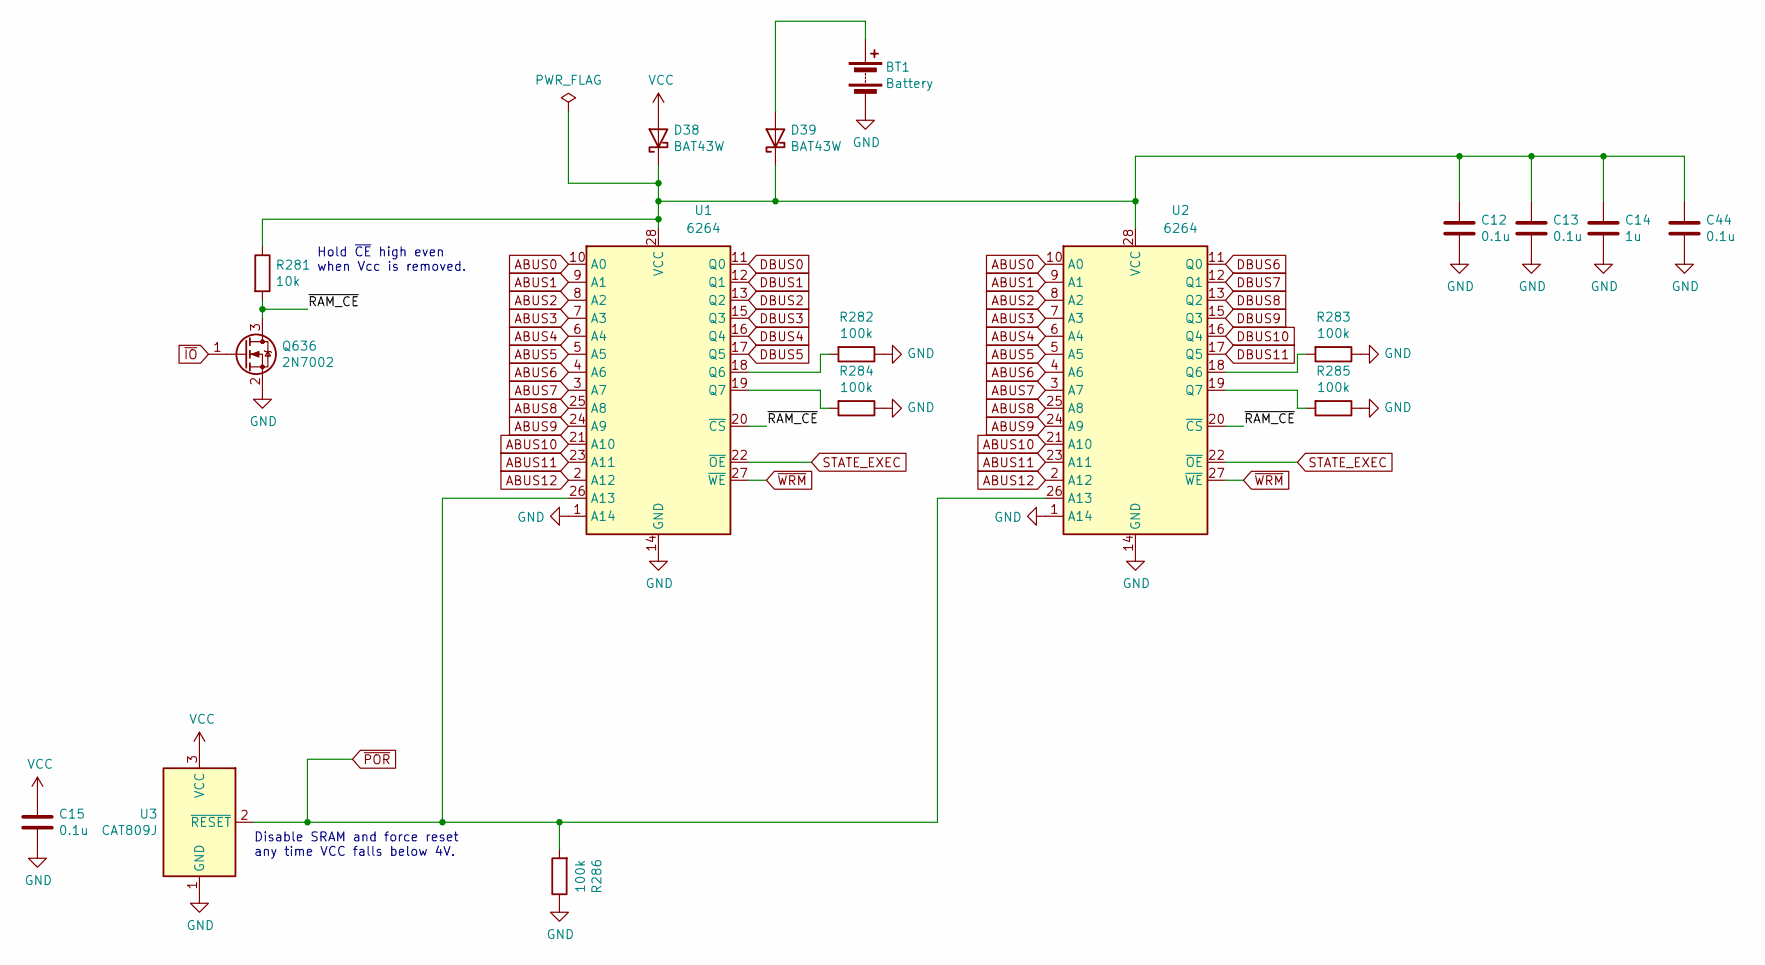
[picture p18: schematic memory.kicad_sch]

Parts:
BT1: Battery; BATTCOM_20MM_PTH; LCSC C964746
C12, C13, C15, C44: 0.1u; C_0805_2012Metric; Part Number CC0805KRX7R9BB104; LCSC C49678
C14: 1u; C_0805_2012Metric; Part Number CL21B105KBFNNNE; LCSC C28323
D38, D39: BAT43W; D_SOD-123; Part Number BAT43W; LCSC C19167
Q636: 2N7002; SOT-23; Part Number 2N7002; LCSC C181083
R281: 10k; R_0603_1608Metric; Part Number 0603WAF1002T5E; LCSC C25804
R282, R283, R284, R285, R286: 100k; R_0603_1608Metric; Part Number 0603WAF1003T5E; LCSC C25803
U1, U2: 6264; SOP-28-330; Part Number LY6264SL-70LLI; LCSC C261872
U3: CAT809J; SOT-23; Part Number CAT809JTBI-GT3; LCSC C328025

Connections:
ABUS0: U1.10 (A0), U2.10 (A0)
ABUS1: U1.9 (A1), U2.9 (A1)
ABUS2: U1.8 (A2), U2.8 (A2)
ABUS3: U1.7 (A3), U2.7 (A3)
ABUS4: U1.6 (A4), U2.6 (A4)
ABUS5: U1.5 (A5), U2.5 (A5)
ABUS6: U1.4 (A6), U2.4 (A6)
ABUS7: U1.3 (A7), U2.3 (A7)
ABUS8: U1.25 (A8), U2.25 (A8)
ABUS9: U1.24 (A9), U2.24 (A9)
ABUS10: U1.21 (A10), U2.21 (A10)
ABUS11: U1.23 (A11), U2.23 (A11)
ABUS12: U1.2 (A12), U2.2 (A12)
DBUS0: U1.11 (Q0)
DBUS1: U1.12 (Q1)
DBUS2: U1.13 (Q2)
DBUS3: U1.15 (Q3)
DBUS4: U1.16 (Q4)
DBUS5: U1.17 (Q5)
DBUS6: U2.11 (Q0)
DBUS7: U2.12 (Q1)
DBUS8: U2.13 (Q2)
DBUS9: U2.15 (Q3)
DBUS10: U2.16 (Q4)
DBUS11: U2.17 (Q5)
GND: BT1.2 (-), C12.1, C13.1, C14.1, C15.1, C44.1, Q636.2 (S), R282.1, R283.1, R284.1, R285.1, R286.1, U1.1 (A14), U1.14 (GND), U2.1 (A14), U2.14 (GND), U3.1 (GND)
unnamed: BT1.1 (+), D39.2 (A)
unnamed: C12.2, C13.2, C14.2, C44.2, D38.1 (K), D39.1 (K), R281.1, U1.28 (VCC), U2.28 (VCC)
unnamed: R282.2, U1.18 (Q6)
unnamed: R283.2, U2.18 (Q6)
unnamed: R284.2, U1.19 (Q7)
unnamed: R285.2, U2.19 (Q7)
STATE_EXEC: U1.22 (~OE), U2.22 (~OE)
VCC: C15.2, D38.2 (A), U3.3 (VCC)
~IO: Q636.1 (G)
~POR: R286.2, U1.26 (A13), U2.26 (A13), U3.2 (~RESET)
~RAM_CE: Q636.3 (D), R281.2, U1.20 (~CS), U2.20 (~CS)
~WRM: U1.27 (~WE), U2.27 (~WE)

Notes on the sheet:
Disable SRAM and force reset any time VCC falls below 4V.
Hold ~{CE} high even when Vcc is removed.
