joewing/q2/hardware/q2/pcb/q2/power.kicad_sch

## KiCad design hardware/q2/pcb/q2/power.kicad_sch (2024-12-15)

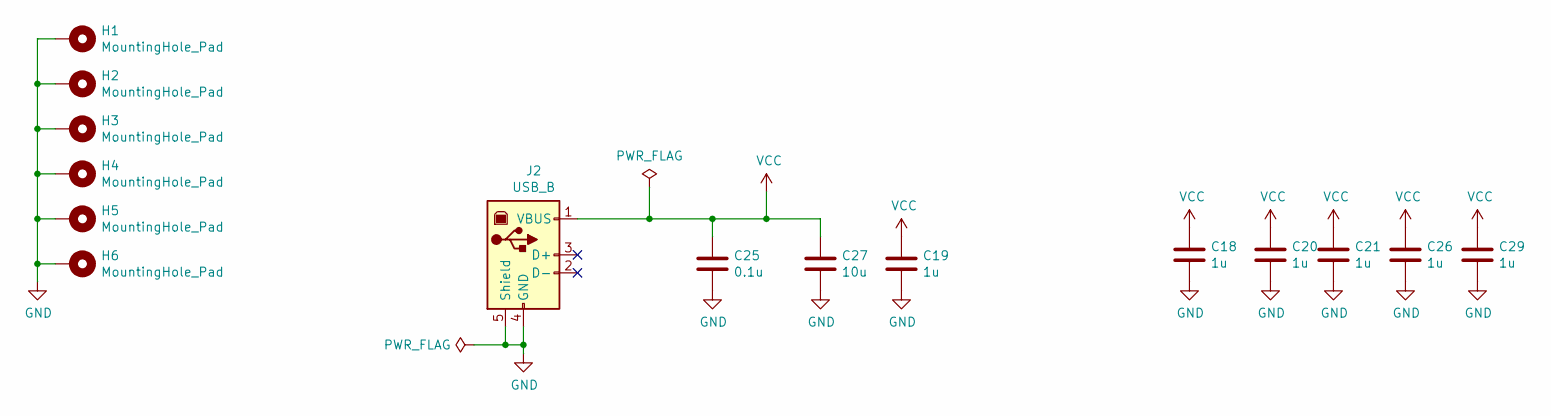
[picture p19: schematic power.kicad_sch]

Parts:
C18, C19, C20, C21, C26, C29: 1u; C_0805_2012Metric; Part Number CL21B105KBFNNNE; LCSC C28323
C25: 0.1u; C_0805_2012Metric; Part Number CC0805KRX7R9BB104; LCSC C49678
C27: 10u; C_0805_2012Metric; Part Number CL21A106KAYNNNE; LCSC C15850
H1, H2, H3, H4, H5, H6: MountingHole_Pad; MountingHole_3.2mm_M3_Pad_Via
J2: USB_B; USB_B_OST_USB-B1HSxx_Horizontal; LCSC C498173

Connections:
GND: C18.1, C19.1, C20.1, C21.1, C25.2, C26.1, C27.1, C29.1, H1.1, H2.1, H3.1, H4.1, H5.1, H6.1, J2.4 (GND), J2.5 (Shield)
VCC: C18.2, C19.2, C20.2, C21.2, C25.1, C26.2, C27.2, C29.2, J2.1 (VBUS)
