joewing/q2/hardware/q2/pcb/q2/preg.kicad_sch

## KiCad design hardware/q2/pcb/q2/preg.kicad_sch (2024-12-15)

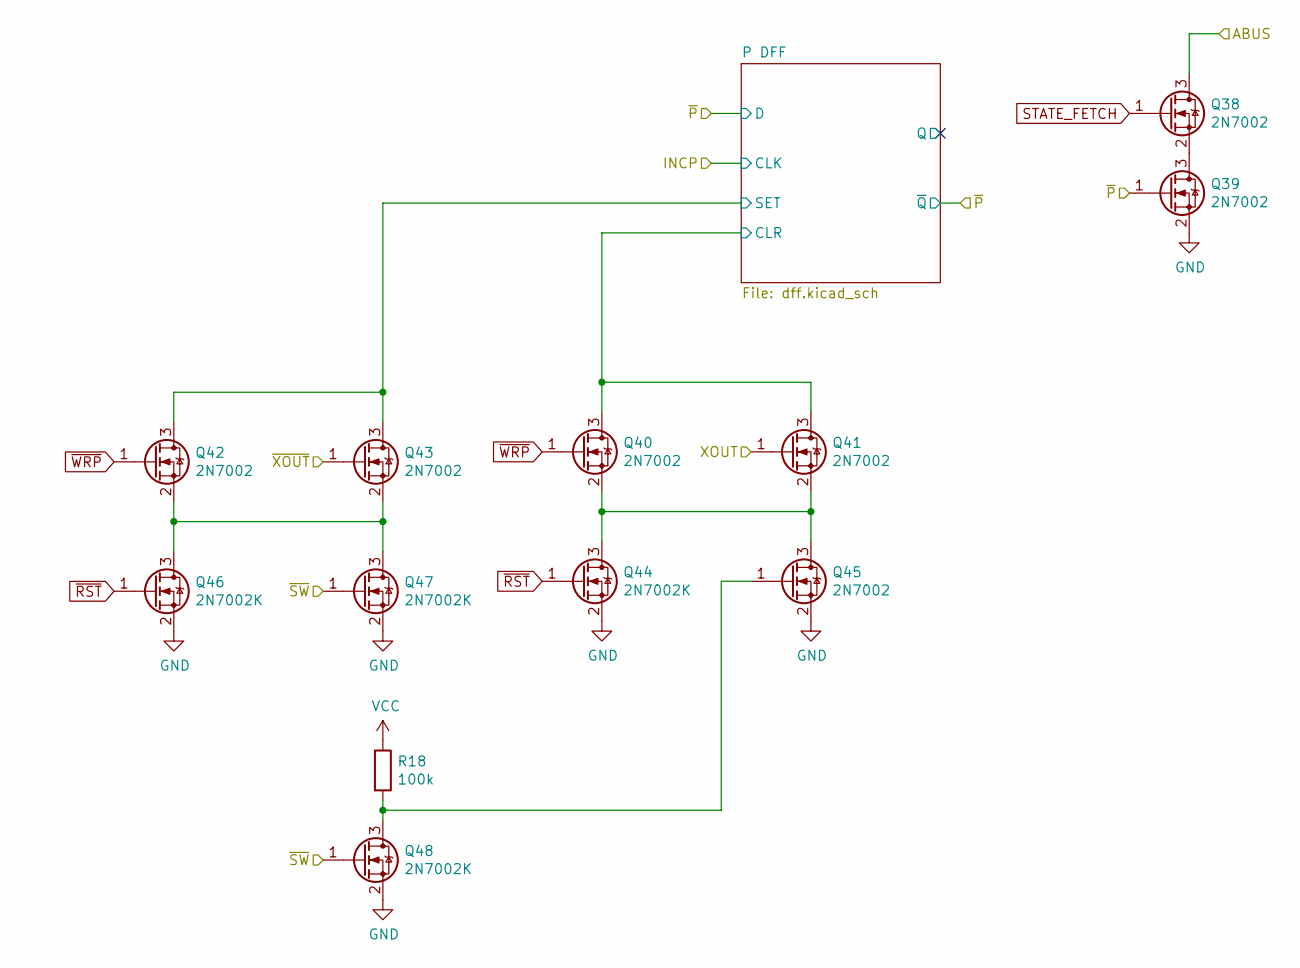
[picture p20: schematic preg.kicad_sch]

Parts:
Q38, Q39, Q40, Q41, Q42, Q43, Q45: 2N7002; SOT-23; Part Number 2N7002; LCSC C181083
Q44, Q46, Q47, Q48: 2N7002K; SOT-23; Part Number 2N7002K; LCSC C181083
R18: 100k; R_0603_1608Metric; Part Number 0603WAF1003T5E; LCSC C25803

Connections:
ABUS: Q38.3 (D)
CLR: Q40.3 (D), Q41.3 (D)
GND: Q39.2 (S), Q44.2 (S), Q45.2 (S), Q46.2 (S), Q47.2 (S), Q48.2 (S)
unnamed: Q38.2 (S), Q39.3 (D)
unnamed: Q40.2 (S), Q41.2 (S), Q44.3 (D), Q45.3 (D)
unnamed: Q42.2 (S), Q43.2 (S), Q46.3 (D), Q47.3 (D)
unnamed: Q45.1 (G), Q48.3 (D), R18.2
SET: Q42.3 (D), Q43.3 (D)
STATE_FETCH: Q38.1 (G)
VCC: R18.1
XOUT: Q41.1 (G)
~P: Q39.1 (G)
~RST: Q44.1 (G), Q46.1 (G)
~SW: Q47.1 (G), Q48.1 (G)
~WRP: Q40.1 (G), Q42.1 (G)
~XOUT: Q43.1 (G)
