joewing/q2/hardware/q2/pcb/q2/programmer.kicad_sch

## KiCad design hardware/q2/pcb/q2/programmer.kicad_sch (2024-12-15)

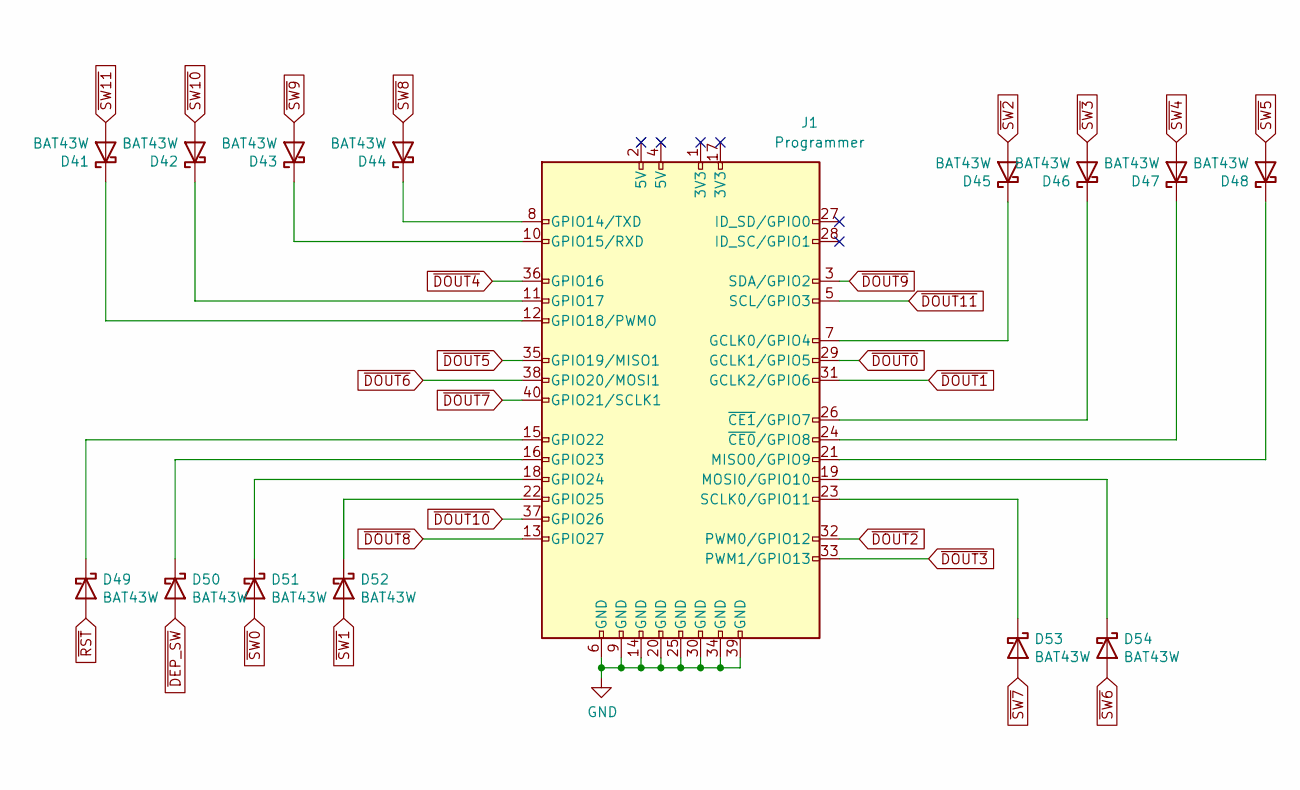
[picture p21: schematic programmer.kicad_sch]

Parts:
D41, D42, D43, D44, D45, D46, D47, D48, D49, D50, D51, D52, D53, D54: BAT43W; D_SOD-123; Part Number BAT43W; LCSC C19167
J1: Programmer; IDC-Header_2x20_P2.54mm_Vertical; Part Number C9138; LCSC C9138

Connections:
GND: J1.6 (GND), J1.9 (GND), J1.14 (GND), J1.20 (GND), J1.25 (GND), J1.30 (GND), J1.34 (GND), J1.39 (GND)
unnamed: D41.1 (K), J1.12 (GPIO18/PWM0)
unnamed: D42.1 (K), J1.11 (GPIO17)
unnamed: D43.1 (K), J1.10 (GPIO15/RXD)
unnamed: D44.1 (K), J1.8 (GPIO14/TXD)
unnamed: D45.1 (K), J1.7 (GCLK0/GPIO4)
unnamed: D46.1 (K), J1.26 (~CE1/GPIO7)
unnamed: D47.1 (K), J1.24 (~CE0/GPIO8)
unnamed: D48.1 (K), J1.21 (MISO0/GPIO9)
unnamed: D49.1 (K), J1.15 (GPIO22)
unnamed: D50.1 (K), J1.16 (GPIO23)
unnamed: D51.1 (K), J1.18 (GPIO24)
unnamed: D52.1 (K), J1.22 (GPIO25)
unnamed: D53.1 (K), J1.23 (SCLK0/GPIO11)
unnamed: D54.1 (K), J1.19 (MOSI0/GPIO10)
~DEP_SW: D50.2 (A)
~DOUT0: J1.29 (GCLK1/GPIO5)
~DOUT1: J1.31 (GCLK2/GPIO6)
~DOUT2: J1.32 (PWM0/GPIO12)
~DOUT3: J1.33 (PWM1/GPIO13)
~DOUT4: J1.36 (GPIO16)
~DOUT5: J1.35 (GPIO19/MISO1)
~DOUT6: J1.38 (GPIO20/MOSI1)
~DOUT7: J1.40 (GPIO21/SCLK1)
~DOUT8: J1.13 (GPIO27)
~DOUT9: J1.3 (SDA/GPIO2)
~DOUT10: J1.37 (GPIO26)
~DOUT11: J1.5 (SCL/GPIO3)
~RST: D49.2 (A)
~SW0: D51.2 (A)
~SW1: D52.2 (A)
~SW2: D45.2 (A)
~SW3: D46.2 (A)
~SW4: D47.2 (A)
~SW5: D48.2 (A)
~SW6: D54.2 (A)
~SW7: D53.2 (A)
~SW8: D44.2 (A)
~SW9: D43.2 (A)
~SW10: D42.2 (A)
~SW11: D41.2 (A)
