joewing/q2/hardware/q2/pcb/q2/slice-high.kicad_sch

## KiCad design hardware/q2/pcb/q2/slice-high.kicad_sch (2024-12-15)

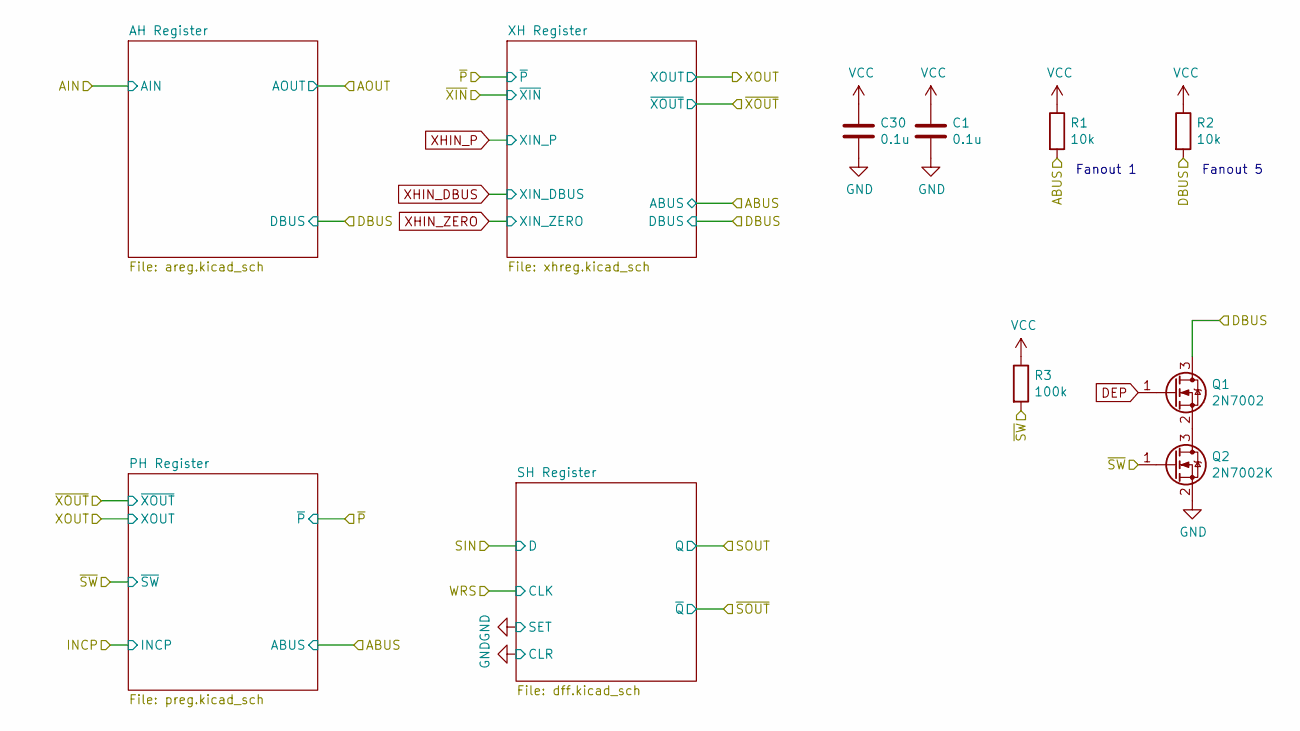
[picture p22: schematic slice-high.kicad_sch]

Parts:
C1, C30: 0.1u; C_0805_2012Metric; Part Number CC0805KRX7R9BB104; LCSC C49678
Q1: 2N7002; SOT-23; Part Number 2N7002; LCSC C181083
Q2: 2N7002K; SOT-23; Part Number 2N7002K; LCSC C181083
R1, R2: 10k; R_0603_1608Metric; Part Number 0603WAF1002T5E; LCSC C25804
R3: 100k; R_0603_1608Metric; Part Number 0603WAF1003T5E; LCSC C25803

Connections:
ABUS: R1.2
DBUS: Q1.3 (D), R2.2
DEP: Q1.1 (G)
GND: C1.2, C30.2, Q2.2 (S)
unnamed: Q1.2 (S), Q2.3 (D)
VCC: C1.1, C30.1, R1.1, R2.1, R3.1
~SW: Q2.1 (G), R3.2

Notes on the sheet:
Fanout 5
Fanout 1
