joewing/q2/hardware/q2/pcb/q2/slice-low.kicad_sch

## KiCad design hardware/q2/pcb/q2/slice-low.kicad_sch (2024-12-15)

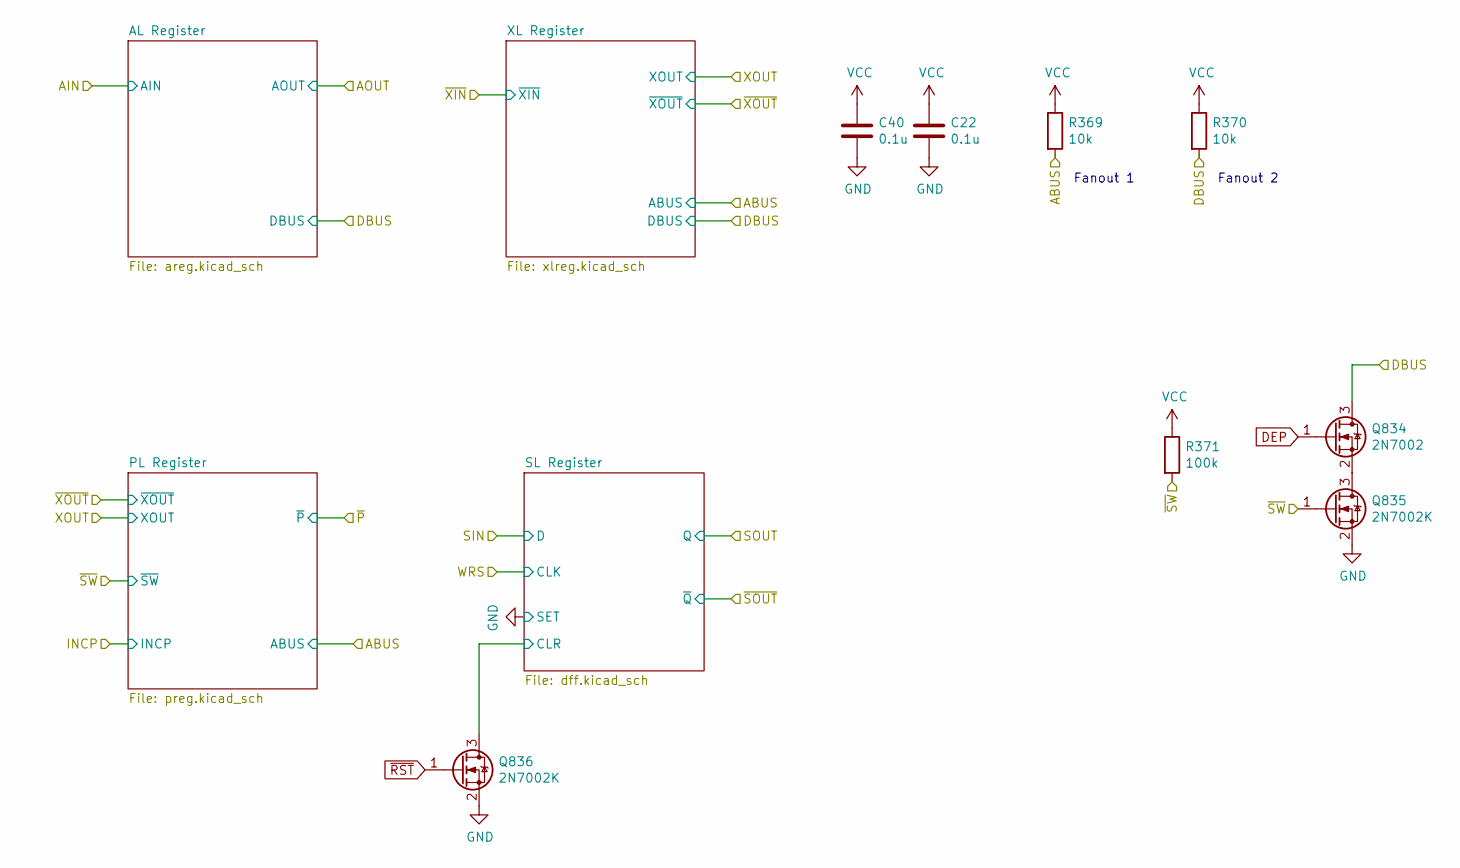
[picture p23: schematic slice-low.kicad_sch]

Parts:
C22, C40: 0.1u; C_0805_2012Metric; Part Number CC0805KRX7R9BB104; LCSC C49678
Q834: 2N7002; SOT-23; Part Number 2N7002; LCSC C181083
Q835, Q836: 2N7002K; SOT-23; Part Number 2N7002K; LCSC C181083
R369, R370: 10k; R_0603_1608Metric; Part Number 0603WAF1002T5E; LCSC C25804
R371: 100k; R_0603_1608Metric; Part Number 0603WAF1003T5E; LCSC C25803

Connections:
ABUS: R369.2
CLR: Q836.3 (D)
DBUS: Q834.3 (D), R370.2
DEP: Q834.1 (G)
GND: C22.2, C40.2, Q835.2 (S), Q836.2 (S)
unnamed: Q834.2 (S), Q835.3 (D)
VCC: C22.1, C40.1, R369.1, R370.1, R371.1
~RST: Q836.1 (G)
~SW: Q835.1 (G), R371.2

Notes on the sheet:
Fanout 1
Fanout 2
