joewing/q2/hardware/q2/pcb/q2/ui.kicad_sch

## KiCad design hardware/q2/pcb/q2/ui.kicad_sch (2024-12-15)

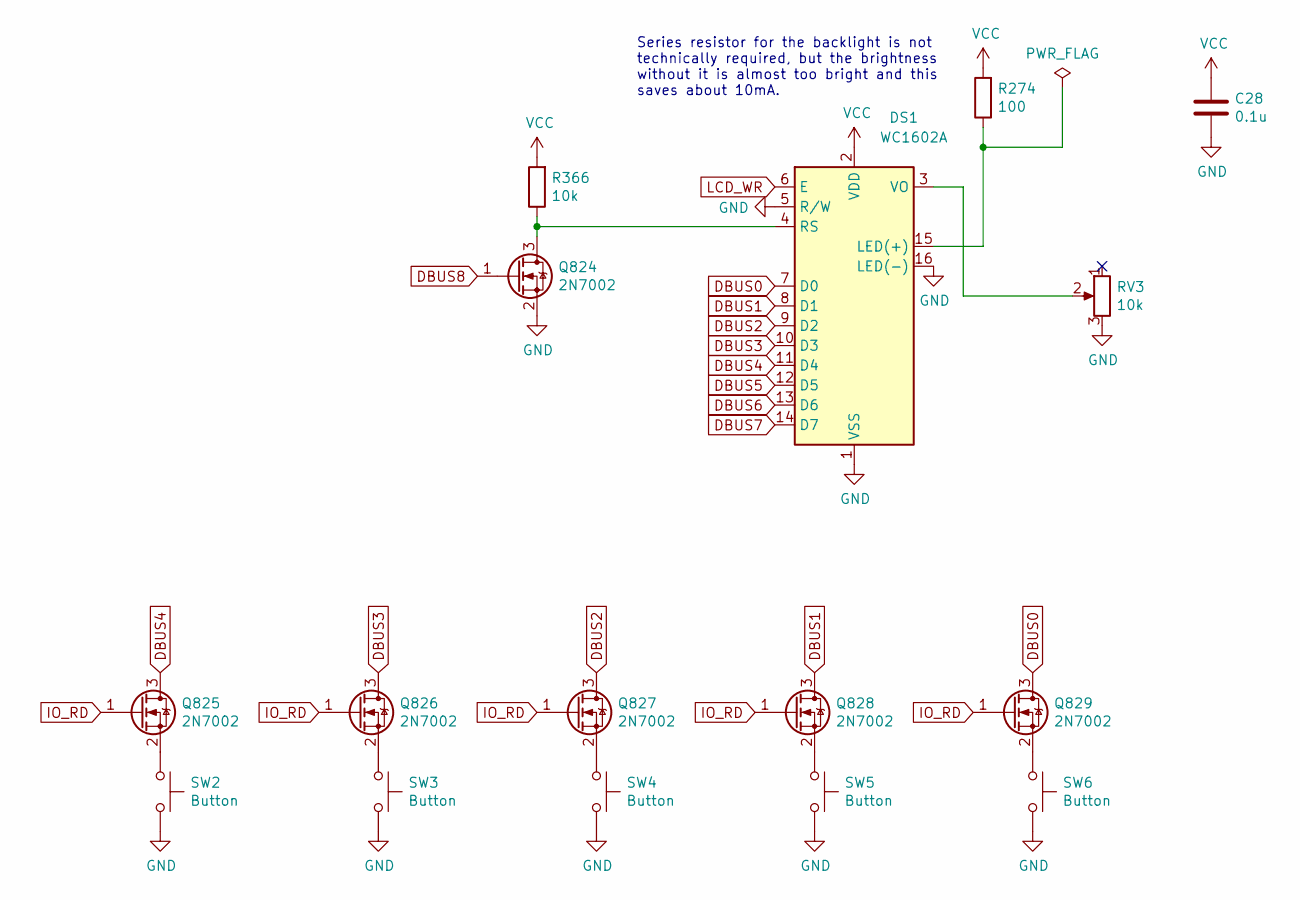
[picture p24: schematic ui.kicad_sch]

Parts:
C28: 0.1u; C_0805_2012Metric; Part Number CC0805KRX7R9BB104; LCSC C49678
DS1: WC1602A
Q824, Q825, Q826, Q827, Q828, Q829: 2N7002; SOT-23; Part Number 2N7002; LCSC C181083
R274: 100; R_1206_3216Metric; Part Number 1206W4F1000T5E; LCSC C17901
R366: 10k; R_0603_1608Metric; Part Number 0603WAF1002T5E; LCSC C25804
RV3: 10k; Potentiometer_Bourns_3386P_Vertical; Part Number 3386P-1-103LF; LCSC C116281
SW2, SW3, SW4, SW5, SW6: Button; SW_SPST_PTS645; Part Number UK-B0228-G5-160-JZ; LCSC C620316

Connections:
DBUS0: DS1.7 (D0), Q829.3 (D)
DBUS1: DS1.8 (D1), Q828.3 (D)
DBUS2: DS1.9 (D2), Q827.3 (D)
DBUS3: DS1.10 (D3), Q826.3 (D)
DBUS4: DS1.11 (D4), Q825.3 (D)
DBUS5: DS1.12 (D5)
DBUS6: DS1.13 (D6)
DBUS7: DS1.14 (D7)
DBUS8: Q824.1 (G)
GND: C28.2, DS1.1 (VSS), DS1.5 (R/W), DS1.16 (LED(-)), Q824.2 (S), RV3.3, SW2.2, SW3.2, SW4.2, SW5.2, SW6.2
IO_RD: Q825.1 (G), Q826.1 (G), Q827.1 (G), Q828.1 (G), Q829.1 (G)
LCD_WR: DS1.6 (E)
unnamed: DS1.3 (VO), RV3.2
unnamed: DS1.4 (RS), Q824.3 (D), R366.1
unnamed: DS1.15 (LED(+)), R274.1
unnamed: Q825.2 (S), SW2.1
unnamed: Q826.2 (S), SW3.1
unnamed: Q827.2 (S), SW4.1
unnamed: Q828.2 (S), SW5.1
unnamed: Q829.2 (S), SW6.1
VCC: C28.1, DS1.2 (VDD), R274.2, R366.2

Notes on the sheet:
Series resistor for the backlight is not technically required, but the brightness without it is almost too bright and this saves about 10mA.
