joewing/q2/hardware/q2/pcb/q2/xhreg.kicad_sch

## KiCad design hardware/q2/pcb/q2/xhreg.kicad_sch (2024-12-15)

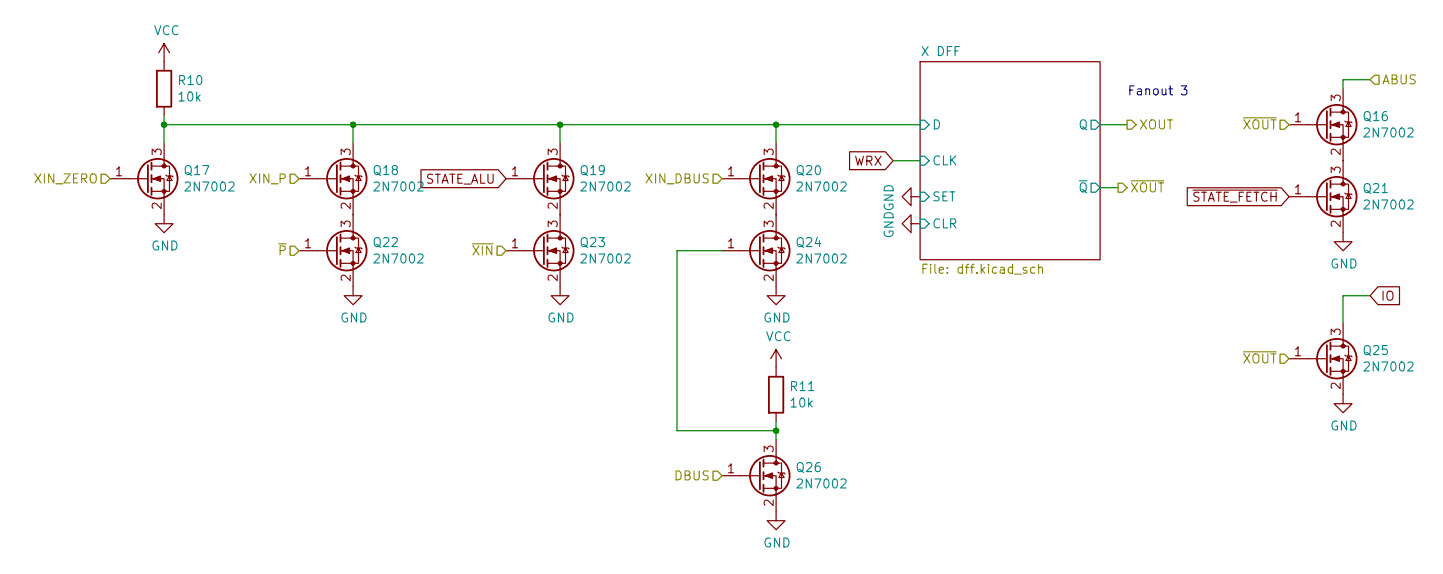
[picture p25: schematic xhreg.kicad_sch]

Parts:
Q16, Q17, Q18, Q19, Q20, Q21, Q22, Q23, Q24, Q25, Q26: 2N7002; SOT-23; Part Number 2N7002; LCSC C181083
R10, R11: 10k; R_0603_1608Metric; Part Number 0603WAF1002T5E; LCSC C25804

Connections:
ABUS: Q16.3 (D)
D: Q17.3 (D), Q18.3 (D), Q19.3 (D), Q20.3 (D), R10.2
DBUS: Q26.1 (G)
GND: Q17.2 (S), Q21.2 (S), Q22.2 (S), Q23.2 (S), Q24.2 (S), Q25.2 (S), Q26.2 (S)
IO: Q25.3 (D)
unnamed: Q16.2 (S), Q21.3 (D)
unnamed: Q18.2 (S), Q22.3 (D)
unnamed: Q19.2 (S), Q23.3 (D)
unnamed: Q20.2 (S), Q24.3 (D)
unnamed: Q24.1 (G), Q26.3 (D), R11.2
STATE_ALU: Q19.1 (G)
VCC: R10.1, R11.1
XIN_DBUS: Q20.1 (G)
XIN_P: Q18.1 (G)
XIN_ZERO: Q17.1 (G)
~P: Q22.1 (G)
~STATE_FETCH: Q21.1 (G)
~XIN: Q23.1 (G)
~XOUT: Q16.1 (G), Q25.1 (G)

Notes on the sheet:
Fanout 3
