joewing/q2/hardware/q2/pcb/q2/xlreg.kicad_sch

## KiCad design hardware/q2/pcb/q2/xlreg.kicad_sch (2024-12-15)

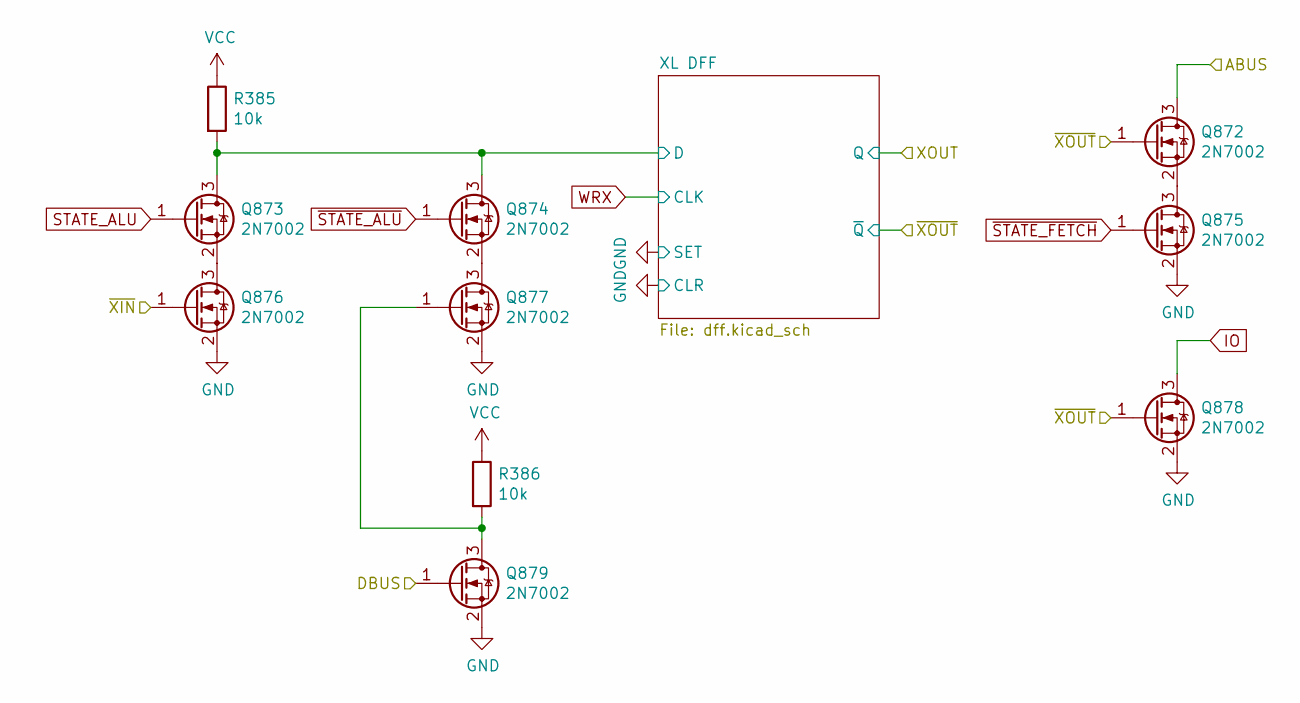
[picture p26: schematic xlreg.kicad_sch]

Parts:
Q872, Q873, Q874, Q875, Q876, Q877, Q878, Q879: 2N7002; SOT-23; Part Number 2N7002; LCSC C181083
R385, R386: 10k; R_0603_1608Metric; Part Number 0603WAF1002T5E; LCSC C25804

Connections:
ABUS: Q872.3 (D)
D: Q873.3 (D), Q874.3 (D), R385.2
DBUS: Q879.1 (G)
GND: Q875.2 (S), Q876.2 (S), Q877.2 (S), Q878.2 (S), Q879.2 (S)
IO: Q878.3 (D)
unnamed: Q872.2 (S), Q875.3 (D)
unnamed: Q873.2 (S), Q876.3 (D)
unnamed: Q874.2 (S), Q877.3 (D)
unnamed: Q877.1 (G), Q879.3 (D), R386.2
STATE_ALU: Q873.1 (G)
VCC: R385.1, R386.1
~STATE_ALU: Q874.1 (G)
~STATE_FETCH: Q875.1 (G)
~XIN: Q876.1 (G)
~XOUT: Q872.1 (G), Q878.1 (G)
