joewing/q2/q2lc/src/symbol.rs

use std::collections::{HashMap, HashSet};

use crate::expr::{Expression, Word};
use crate::Machine;

#[derive(Hash, PartialEq, Eq, Clone)]
pub enum Symbol {
    Function(Word, Vec<Word>),
    Constant(Word),
    Label(String),
}

struct Scope {
    symbols: HashMap<String, Symbol>,
    watermark: Word,
    stack: Word,
    return_address: Symbol,
    break_label: Option<String>,
}

pub struct SymbolTable {
    code: Vec<String>,
    words: Word,
    data: Vec<(String, Vec<Symbol>)>,
    immediates: HashMap<Symbol, String>,
    local_labels: HashSet<String>,
    scopes: Vec<Scope>,
    index: usize,
    page: Word,
    heap: Word,
    code_start: Word,
    heap_start: Word,
}

fn overlaps(a0: Word, a1: Word, b0: Word, b1: Word) -> bool {
    (b0 > a0 && b0 < a1) || (b1 > a0 && b1 < a1)
}

impl SymbolTable {

    pub const PAGE_SIZE: Word = 128;
    pub const PAGE_COUNT: Word = 32;
    pub const ENTRYPOINT: &'static str = "main";
    const BASE_WATERMARK: Word = 0x004;

    pub fn new(machine: &Machine) -> SymbolTable {
        let global_scope = Scope {
            symbols: HashMap::new(),
            watermark: SymbolTable::BASE_WATERMARK,
            stack: SymbolTable::BASE_WATERMARK,
            return_address: Symbol::Constant(0),
            break_label: None,
        };
        SymbolTable {
            code: Vec::new(),
            data: Vec::new(),
            immediates: HashMap::new(),
            scopes: vec![global_scope],
            local_labels: HashSet::new(),
            words: 0,
            index: 0,
            page: (machine.code_addr as Word) / SymbolTable::PAGE_SIZE as Word,
            heap: machine.heap_addr as Word,
            heap_start: machine.heap_addr as Word,
            code_start: machine.code_addr as Word
        }
    }

    fn append(&mut self, line: String) {
        self.code.push(line);
    }

    fn extend(&mut self, lines: Vec<String>) {
        for line in lines {
            self.append(line);
        }
    }

    fn finish_page(&mut self) {
        let mut temp = Vec::new();
        for (symbol, label) in self.immediates.iter() {
            temp.push(format!("{}:", label));
            let s = match symbol {
                Symbol::Label(s) => s.clone(),
                Symbol::Constant(w) => (w & 0xFFF).to_string(),
                _ => panic!("undefined immediate: {}", label)
            };
            temp.push(format!("  .dw {}", s));
        }
        self.extend(temp);
        self.local_labels.clear();
        self.immediates.clear();
    }

    fn new_page(&mut self) {
        self.finish_page();
        self.append(format!("  .align"));
        self.words = 0;
        self.page += 1;
    }

    fn check_size(&self) -> Result<(), String> {
        if self.scopes.len() != 1 {
            return Err(format!("invalid state"));
        }
        let scope = self.scopes.last().unwrap();
        let total_words = SymbolTable::PAGE_COUNT * SymbolTable::PAGE_SIZE - 1;
        let heap_usage = self.heap_start - self.heap;
        let code_end = self.page * SymbolTable::PAGE_SIZE;
        let code_usage = code_end - self.code_start;
        let max_code = total_words - self.code_start;
        let usage = heap_usage + code_usage + scope.watermark;
        println!("memory usage:    {:4} / {:4}", usage, total_words);
        println!("zero-page words: {:4} / {:4}", scope.watermark, SymbolTable::PAGE_SIZE);
        println!("code words:      {:4} / {:4}", code_usage, max_code);
        println!("heap words:      {:4} / {:4}", heap_usage, self.heap_start);
        if scope.watermark > SymbolTable::PAGE_SIZE {
            return Err(format!("too many vars: {}", scope.watermark));
        }
        if self.page - 1 > SymbolTable::PAGE_COUNT {
            return Err(format!("code requires too many pages: {}", self.page));
        }
        if overlaps(self.heap, self.heap_start, self.code_start, code_end) {
            return Err(format!("code and heap overlap"))
        }
        Ok(())
    }

    pub fn emit_prelude(&mut self, machine: &Machine) -> Result<(), String> {
        if machine.code_addr < 128 {
            // Bootstrap.
            // This will just run the program over and over.
            self.append(format!("  .org {}", machine.code_addr));
            self.append_word(format!("  lea =0"));
            self.append_word(format!("  jmp @$+1"));
            self.append_word(format!("  .dw {}", SymbolTable::ENTRYPOINT));

            // Entry point.
            // This will return to the bootstrap page.
            self.new_page();
            let entrypoint_label = self.append_immediate(&Symbol::Label(SymbolTable::ENTRYPOINT.to_string()));
            let field0_label = self.append_immediate(&Symbol::Constant(0xC00));
            let neg1_label = self.append_immediate(&Symbol::Constant(0xFFF));
            self.append_word(format!("  lea $+2"));
            self.append_word(format!("  jmp @{}", entrypoint_label));
            self.append_word(format!("  lda {}", field0_label));
            self.append_word(format!("  sta @{}", neg1_label));
            self.append_word(format!("  jmp =0"));
        } else {
            self.append(format!("  .org {}", machine.code_addr));
            let entrypoint_label = self.append_immediate(&Symbol::Label(SymbolTable::ENTRYPOINT.to_string()));
            self.append_word(format!("  lea $"));
            self.append_word(format!("  jmp @{}", entrypoint_label));
        }
        Ok(())
    }

    pub fn emit(&mut self) -> Result<Vec<String>, String> {
        let mut result = Vec::new();
        self.finish_page();
        result.extend(self.code.iter().cloned());
        for (label, symbols) in self.data.iter() {
            result.push(format!("{}:", label));
            for symbol in symbols {
                let value = match symbol {
                    Symbol::Label(label) => label.clone(),
                    Symbol::Constant(w) => w.to_string(),
                    _ => panic!("internal error"),
                };
                result.push(format!("  .dw {}", value));
                self.words += 1;
                if self.words >= SymbolTable::PAGE_SIZE {
                    self.page += 1;
                    self.words -= SymbolTable::PAGE_SIZE;
                }
            }
        }
        while self.words > 0 {
            self.page += 1;
            let delta = Word::min(self.words, SymbolTable::PAGE_SIZE);
            self.words -= delta;
        }
        self.data.clear();
        let _ = self.check_size()?;
        Ok(result)
    }

    fn advance(&mut self) {
        // We need to leave room for:
        //  - The word being emitted.
        //  - An immediate value stored in the same page.
        //  - The jump instruction to the next page.
        //  - A pointer to the next page.
        if self.words + 4 > SymbolTable::PAGE_SIZE {
            let page_label = self.next_label();
            self.append(format!("  jmp @$+1"));
            self.append(format!("  .dw {}", page_label));
            self.new_page();
            self.append_label(&page_label);
        }
        self.words += 1;
    }

    pub fn append_code_indirect(&mut self, opcode: &str, symbol: &Symbol) -> Result<(), String> {
        self.advance();
        let operand_str = self.emit_operand(symbol);
        self.append(format!("  {} @{}", opcode, operand_str));
        Ok(())
    }

    pub fn append_code_immediate(&mut self, opcode: &str, word: Word) -> Result<(), String> {
        self.advance();
        let operand_str = self.append_immediate(&Symbol::Constant(word));
        self.append(format!("  {} {}", opcode, operand_str));
        Ok(())
    }

    pub fn append_code(&mut self, opcode: &str, symbol: &Symbol) -> Result<(), String> {
        self.advance();
        let operand_str = self.emit_operand(symbol);
        self.append(format!("  {} {}", opcode, operand_str));
        Ok(())
    }

    fn emit_operand(&mut self, symbol: &Symbol) -> String {
        match symbol {
            Symbol::Constant(w) if *w < SymbolTable::PAGE_SIZE => format!("={}", w),
            Symbol::Label(s) if self.local_labels.contains(s) => s.clone(),
            _ => format!("@{}", self.append_immediate(symbol)),
        }
    }

    fn append_immediate(&mut self, symbol: &Symbol) -> String {
        let label_opt = self.immediates.get(symbol).map(|x| x.clone());
        if let Some(label) = label_opt {
            label
        } else {
            let label = self.next_label();
            self.immediates.insert(symbol.clone(), label.clone());
            self.words += 1;
            label
        }
    }

    fn append_word(&mut self, value: String) {
        self.append(value);
        self.words += 1;
    }

    pub fn append_label(&mut self, label: &String) {
        self.local_labels.insert(label.clone());
        self.append(format!("{}:", label));
    }

    pub fn return_address(&self) -> Symbol {
        self.scopes.last().unwrap().return_address.clone()
    }

    pub fn break_label(&self) -> Result<String, String> {
        let last = self.scopes.last().unwrap();
        match &last.break_label {
            Some(s) => Ok(s.clone()),
            None => Err(format!("break not in a loop"))
        }
    }

    pub fn next_label(&mut self) -> String {
        self.index += 1;
        let label = format!("L{}", self.index);
        label
    }

    pub fn append_data(&mut self, exprs: &Vec<Expression>) -> Result<Symbol, String> {
        let mut data = Vec::new();
        for expr in exprs {
            let value = match expr {
                Expression::Constant(w) => Symbol::Constant(*w),
                Expression::Symbol(name) => {
                    let symbol = self.lookup(name)?;
                    match symbol {
                        Symbol::Constant(w) => Symbol::Constant(w),
                        Symbol::Label(s) => Symbol::Label(s),
                        Symbol::Function(_, _) => {
                            Symbol::Label(name.clone())
                        },
                    }
                },
                Expression::ArrayLiteral(inner) => self.append_data(inner)?,
                _ => {
                    return Err(format!("array literal must be constant"));
                },
            };
            data.push(value);
        }
        let label = self.next_label();
        self.data.push((label.clone(), data));
        Ok(Symbol::Label(label))
    }

    pub fn append_heap(&mut self, size: Word) -> Result<Word, String> {
        self.heap = match self.heap.overflowing_sub(size) {
            (v, false) => v,
            (_, true) => {
                return Err(format!("out of heap space"));
            },
        };
        Ok(self.heap)
    }

    pub fn enter(&mut self) {
        let last = self.scopes.last().unwrap();
        let watermark = last.watermark;
        let return_address = last.return_address.clone();
        let break_label = last.break_label.clone();
        self.scopes.push(
            Scope {
                symbols: HashMap::new(),
                watermark: watermark,
                stack: watermark,
                return_address: return_address,
                break_label: break_label,
            }
        );
    }

    pub fn leave(&mut self) {
        let last = self.scopes.pop().unwrap();
        let current = self.scopes.last_mut().unwrap();
        current.watermark = Word::max(last.watermark, current.watermark);
    }

    /** Update current stack to account for an argument to a function call. */
    pub fn update_stack(&mut self, param: Word) {
        let last = self.scopes.last_mut().unwrap();
        last.stack = Word::max(last.stack, param + 1);
        last.watermark = Word::max(last.watermark, last.stack);
    }

    pub fn enter_loop(&mut self, break_label: &String) {
        let last = self.scopes.last().unwrap();
        let watermark = last.watermark;
        let return_address = last.return_address.clone();
        self.scopes.push(
            Scope {
                symbols: HashMap::new(),
                watermark: watermark,
                stack: watermark,
                return_address: return_address,
                break_label: Some(break_label.clone()),
            }
        );
    }

    pub fn leave_loop(&mut self) -> Result<(), String> {
        let break_label = self.break_label()?;
        self.leave();
        self.append_label(&break_label);
        Ok(())
    }

    pub fn enter_function(&mut self, watermark: Word) -> Symbol {
        self.scopes.push(
            Scope {
                symbols: HashMap::new(),
                watermark: watermark,
                stack: watermark,
                return_address: Symbol::Constant(0),
                break_label: None,
            }
        );
        let return_address = self.allocate_temp();
        self.scopes.last_mut().unwrap().return_address = return_address.clone();
        return_address
    }

    pub fn leave_function(&mut self, name: &String, args: Vec<Word>) {
        let func_scope = self.scopes.pop().unwrap();
        let watermark = func_scope.watermark;
        let symbol = Symbol::Function(watermark, args);
        let scope = self.scopes.last_mut().unwrap();
        scope.watermark = Word::max(scope.watermark, watermark);
        scope.symbols.insert(name.clone(), symbol);
    }

    pub fn allocate_temp(&mut self) -> Symbol {
        let scope = self.scopes.last_mut().unwrap();
        let addr = scope.stack;
        scope.stack += 1;
        scope.watermark = Word::max(scope.watermark, scope.stack);
        Symbol::Constant(addr)
    }

    pub fn release_temp(&mut self) {
        self.scopes.last_mut().unwrap().stack -= 1;
    }

    pub fn current_watermark(&self) -> Word {
        self.scopes.last().unwrap().stack
    }

    pub fn declare_var(&mut self, name: &String, value: Option<Symbol>) -> Result<(), String> {
        let symbol = if self.is_global() {
            if value.is_some() {
                Err(format!("global var ({}) cannot have an initial value", name))
            } else {
                let addr = self.append_heap(1)?;
                Ok(Symbol::Constant(addr))
            }
        } else {
            Ok(self.allocate_temp())
        }?;
        let scope = self.scopes.last_mut().unwrap();
        scope.symbols.insert(name.clone(), symbol);
        Ok(())
    }

    pub fn declare_const(&mut self, name: &String, symbol: Symbol) {
        let scope = self.scopes.last_mut().unwrap();
        scope.symbols.insert(name.clone(), symbol);
    }

    pub fn declare_arg(&mut self, name: &String) -> Word {
        let addr = self.allocate_temp();
        let scope = self.scopes.last_mut().unwrap();
        scope.symbols.insert(name.clone(), addr.clone());
        if let Symbol::Constant(w) = addr {
            w
        } else {
            panic!("internal error")
        }
    }

    pub fn lookup(&self, name: &String) -> Result<Symbol, String> {
        for scope in self.scopes.iter() {
            match scope.symbols.get(name) {
                Some(s) => return Ok(s.clone()),
                None => ()
            }
        }
        Err(format!("undefined: {}", name))
    }

    pub fn is_global(&self) -> bool {
        self.scopes.last().unwrap().return_address == Symbol::Constant(0)
    }
}
